Agilack/probe-net-serial/ext-display/sw-firmware/efm8bb1_defs.h

//------------------------------------------------------------------------------
// Copyright 2014 Silicon Laboratories, Inc.
// All rights reserved. This program and the accompanying materials
// are made available under the terms of the Silicon Laboratories End User
// License Agreement which accompanies this distribution, and is available at
// http://developer.silabs.com/legal/version/v11/Silicon_Labs_Software_License_Agreement.txt
// Original content and implementation provided by Silicon Laboratories.
//------------------------------------------------------------------------------
//Supported Devices:
//  EFM8BB10F2G
//  EFM8BB10F4G
//  EFM8BB10F8G
//  EFM8BB10F8G
//  EFM8BB10F8G

#ifndef SI_EFM8BB1_REGISTER_ENUMS_H
#define SI_EFM8BB1_REGISTER_ENUMS_H

//------------------------------------------------------------------------------
// ADC0AC Enums (ADC0 Accumulator Configuration @ 0xB3)
//------------------------------------------------------------------------------
#define ADC0AC_ADRPT__FMASK            0x07 ///< Repeat Count                                      
#define ADC0AC_ADRPT__SHIFT            0x00 ///< Repeat Count                                      
#define ADC0AC_ADRPT__ACC_1            0x00 ///< Perform and Accumulate 1 conversion (not used in  
                                            ///< 12-bit mode).                                     
#define ADC0AC_ADRPT__ACC_4            0x01 ///< Perform and Accumulate 4 conversions (1 conversion
                                            ///< in 12-bit mode).                                  
#define ADC0AC_ADRPT__ACC_8            0x02 ///< Perform and Accumulate 8 conversions (2           
                                            ///< conversions in 12-bit mode).                      
#define ADC0AC_ADRPT__ACC_16           0x03 ///< Perform and Accumulate 16 conversions (4          
                                            ///< conversions in 12-bit mode).                      
#define ADC0AC_ADRPT__ACC_32           0x04 ///< Perform and Accumulate 32 conversions (8          
                                            ///< conversions in 12-bit mode).                      
#define ADC0AC_ADRPT__ACC_64           0x05 ///< Perform and Accumulate 64 conversions (16         
                                            ///< conversions in 12-bit mode).                      
                                                                                                   
#define ADC0AC_ADSJST__FMASK           0x38 ///< Accumulator Shift and Justify                     
#define ADC0AC_ADSJST__SHIFT           0x03 ///< Accumulator Shift and Justify                     
#define ADC0AC_ADSJST__RIGHT_NO_SHIFT  0x00 ///< Right justified. No shifting applied.             
#define ADC0AC_ADSJST__RIGHT_SHIFT_1   0x08 ///< Right justified. Shifted right by 1 bit.          
#define ADC0AC_ADSJST__RIGHT_SHIFT_2   0x10 ///< Right justified. Shifted right by 2 bits.         
#define ADC0AC_ADSJST__RIGHT_SHIFT_3   0x18 ///< Right justified. Shifted right by 3 bits.         
#define ADC0AC_ADSJST__LEFT_NO_SHIFT   0x20 ///< Left justified. No shifting applied.              
                                                                                                   
#define ADC0AC_ADAE__BMASK             0x40 ///< Accumulate Enable                                 
#define ADC0AC_ADAE__SHIFT             0x06 ///< Accumulate Enable                                 
#define ADC0AC_ADAE__ACC_DISABLED      0x00 ///< ADC0H:ADC0L contain the result of the latest      
                                            ///< conversion when Burst Mode is disabled.           
#define ADC0AC_ADAE__ACC_ENABLED       0x40 ///< ADC0H:ADC0L contain the accumulated conversion    
                                            ///< results when Burst Mode is disabled. Firmware must
                                            ///< write 0x0000 to ADC0H:ADC0L to clear the          
                                            ///< accumulated result.                               
                                                                                                   
#define ADC0AC_AD12BE__BMASK           0x80 ///< 12-Bit Mode Enable                                
#define ADC0AC_AD12BE__SHIFT           0x07 ///< 12-Bit Mode Enable                                
#define ADC0AC_AD12BE__12_BIT_DISABLED 0x00 ///< Disable 12-bit mode.                              
#define ADC0AC_AD12BE__12_BIT_ENABLED  0x80 ///< Enable 12-bit mode.                               
                                                                                                   
//------------------------------------------------------------------------------
// ADC0CF Enums (ADC0 Configuration @ 0xBC)
//------------------------------------------------------------------------------
#define ADC0CF_ADGN__BMASK         0x01 ///< Gain Control                                      
#define ADC0CF_ADGN__SHIFT         0x00 ///< Gain Control                                      
#define ADC0CF_ADGN__GAIN_0P5      0x00 ///< The on-chip PGA gain is 0.5.                      
#define ADC0CF_ADGN__GAIN_1        0x01 ///< The on-chip PGA gain is 1.                        
                                                                                               
#define ADC0CF_ADTM__BMASK         0x02 ///< Track Mode                                        
#define ADC0CF_ADTM__SHIFT         0x01 ///< Track Mode                                        
#define ADC0CF_ADTM__TRACK_NORMAL  0x00 ///< Normal Track Mode. When ADC0 is enabled,          
                                        ///< conversion begins immediately following the start-
                                        ///< of-conversion signal.                             
#define ADC0CF_ADTM__TRACK_DELAYED 0x02 ///< Delayed Track Mode. When ADC0 is enabled,         
                                        ///< conversion begins 4 SAR clock cycles following the
                                        ///< start-of-conversion signal. The ADC is allowed to 
                                        ///< track during this time.                           
                                                                                               
#define ADC0CF_AD8BE__BMASK        0x04 ///< 8-Bit Mode Enable                                 
#define ADC0CF_AD8BE__SHIFT        0x02 ///< 8-Bit Mode Enable                                 
#define ADC0CF_AD8BE__NORMAL       0x00 ///< ADC0 operates in 10-bit or 12-bit mode (normal    
                                        ///< operation).                                       
#define ADC0CF_AD8BE__8_BIT        0x04 ///< ADC0 operates in 8-bit mode.                      
                                                                                               
#define ADC0CF_ADSC__FMASK         0xF8 ///< SAR Clock Divider                                 
#define ADC0CF_ADSC__SHIFT         0x03 ///< SAR Clock Divider                                 
                                                                                               
//------------------------------------------------------------------------------
// ADC0CN0 Enums (ADC0 Control 0 @ 0xE8)
//------------------------------------------------------------------------------
#define ADC0CN0_ADCM__FMASK            0x07 ///< Start of Conversion Mode Select                   
#define ADC0CN0_ADCM__SHIFT            0x00 ///< Start of Conversion Mode Select                   
#define ADC0CN0_ADCM__ADBUSY           0x00 ///< ADC0 conversion initiated on write of 1 to ADBUSY.
#define ADC0CN0_ADCM__TIMER0           0x01 ///< ADC0 conversion initiated on overflow of Timer 0. 
#define ADC0CN0_ADCM__TIMER2           0x02 ///< ADC0 conversion initiated on overflow of Timer 2. 
#define ADC0CN0_ADCM__TIMER3           0x03 ///< ADC0 conversion initiated on overflow of Timer 3. 
#define ADC0CN0_ADCM__CNVSTR           0x04 ///< ADC0 conversion initiated on rising edge of       
                                            ///< CNVSTR.                                           
                                                                                                   
#define ADC0CN0_ADWINT__BMASK          0x08 ///< Window Compare Interrupt Flag                     
#define ADC0CN0_ADWINT__SHIFT          0x03 ///< Window Compare Interrupt Flag                     
#define ADC0CN0_ADWINT__NOT_SET        0x00 ///< An ADC window compare event did not occur.        
#define ADC0CN0_ADWINT__SET            0x08 ///< An ADC window compare event occurred.             
                                                                                                   
#define ADC0CN0_ADBUSY__BMASK          0x10 ///< ADC Busy                                          
#define ADC0CN0_ADBUSY__SHIFT          0x04 ///< ADC Busy                                          
#define ADC0CN0_ADBUSY__NOT_SET        0x00 ///< An ADC0 conversion is not currently in progress.  
#define ADC0CN0_ADBUSY__SET            0x10 ///< ADC0 conversion is in progress or start an ADC0   
                                            ///< conversion.                                       
                                                                                                   
#define ADC0CN0_ADINT__BMASK           0x20 ///< Conversion Complete Interrupt Flag                
#define ADC0CN0_ADINT__SHIFT           0x05 ///< Conversion Complete Interrupt Flag                
#define ADC0CN0_ADINT__NOT_SET         0x00 ///< ADC0 has not completed a conversion since the last
                                            ///< time ADINT was cleared.                           
#define ADC0CN0_ADINT__SET             0x20 ///< ADC0 completed a data conversion.                 
                                                                                                   
#define ADC0CN0_ADBMEN__BMASK          0x40 ///< Burst Mode Enable                                 
#define ADC0CN0_ADBMEN__SHIFT          0x06 ///< Burst Mode Enable                                 
#define ADC0CN0_ADBMEN__BURST_DISABLED 0x00 ///< Disable ADC0 burst mode.                          
#define ADC0CN0_ADBMEN__BURST_ENABLED  0x40 ///< Enable ADC0 burst mode.                           
                                                                                                   
#define ADC0CN0_ADEN__BMASK            0x80 ///< ADC Enable                                        
#define ADC0CN0_ADEN__SHIFT            0x07 ///< ADC Enable                                        
#define ADC0CN0_ADEN__DISABLED         0x00 ///< Disable ADC0 (low-power shutdown).                
#define ADC0CN0_ADEN__ENABLED          0x80 ///< Enable ADC0 (active and ready for data            
                                            ///< conversions).                                     
                                                                                                   
//------------------------------------------------------------------------------
// ADC0CN1 Enums (ADC0 Control 1 @ 0xB2)
//------------------------------------------------------------------------------
#define ADC0CN1_ADCMBE__BMASK              0x01 ///< Common Mode Buffer Enable                         
#define ADC0CN1_ADCMBE__SHIFT              0x00 ///< Common Mode Buffer Enable                         
#define ADC0CN1_ADCMBE__CM_BUFFER_DISABLED 0x00 ///< Disable the common mode buffer. This setting      
                                                ///< should be used only if the tracking time of the   
                                                ///< signal is greater than 1.5 us.                    
#define ADC0CN1_ADCMBE__CM_BUFFER_ENABLED  0x01 ///< Enable the common mode buffer. This setting should
                                                ///< be used in most cases, and will give the best     
                                                ///< dynamic ADC performance. The common mode buffer   
                                                ///< must be enabled if signal tracking time is less   
                                                ///< than or equal to 1.5 us.                          
                                                                                                       
//------------------------------------------------------------------------------
// ADC0GTH Enums (ADC0 Greater-Than High Byte @ 0xC4)
//------------------------------------------------------------------------------
#define ADC0GTH_ADC0GTH__FMASK 0xFF ///< Greater-Than High Byte
#define ADC0GTH_ADC0GTH__SHIFT 0x00 ///< Greater-Than High Byte
                                                               
//------------------------------------------------------------------------------
// ADC0GTL Enums (ADC0 Greater-Than Low Byte @ 0xC3)
//------------------------------------------------------------------------------
#define ADC0GTL_ADC0GTL__FMASK 0xFF ///< Greater-Than Low Byte
#define ADC0GTL_ADC0GTL__SHIFT 0x00 ///< Greater-Than Low Byte
                                                              
//------------------------------------------------------------------------------
// ADC0H Enums (ADC0 Data Word High Byte @ 0xBE)
//------------------------------------------------------------------------------
#define ADC0H_ADC0H__FMASK 0xFF ///< Data Word High Byte
#define ADC0H_ADC0H__SHIFT 0x00 ///< Data Word High Byte
                                                        
//------------------------------------------------------------------------------
// ADC0L Enums (ADC0 Data Word Low Byte @ 0xBD)
//------------------------------------------------------------------------------
#define ADC0L_ADC0L__FMASK 0xFF ///< Data Word Low Byte
#define ADC0L_ADC0L__SHIFT 0x00 ///< Data Word Low Byte
                                                       
//------------------------------------------------------------------------------
// ADC0LTH Enums (ADC0 Less-Than High Byte @ 0xC6)
//------------------------------------------------------------------------------
#define ADC0LTH_ADC0LTH__FMASK 0xFF ///< Less-Than High Byte
#define ADC0LTH_ADC0LTH__SHIFT 0x00 ///< Less-Than High Byte
                                                            
//------------------------------------------------------------------------------
// ADC0LTL Enums (ADC0 Less-Than Low Byte @ 0xC5)
//------------------------------------------------------------------------------
#define ADC0LTL_ADC0LTL__FMASK 0xFF ///< Less-Than Low Byte
#define ADC0LTL_ADC0LTL__SHIFT 0x00 ///< Less-Than Low Byte
                                                           
//------------------------------------------------------------------------------
// ADC0MX Enums (ADC0 Multiplexer Selection @ 0xBB)
//------------------------------------------------------------------------------
#define ADC0MX_ADC0MX__FMASK   0x1F ///< AMUX0 Positive Input Selection
#define ADC0MX_ADC0MX__SHIFT   0x00 ///< AMUX0 Positive Input Selection
#define ADC0MX_ADC0MX__ADC0P0  0x00 ///< Select ADC0.0.                
#define ADC0MX_ADC0MX__ADC0P1  0x01 ///< Select ADC0.1.                
#define ADC0MX_ADC0MX__ADC0P2  0x02 ///< Select ADC0.2.                
#define ADC0MX_ADC0MX__ADC0P3  0x03 ///< Select ADC0.3.                
#define ADC0MX_ADC0MX__ADC0P4  0x04 ///< Select ADC0.4.                
#define ADC0MX_ADC0MX__ADC0P5  0x05 ///< Select ADC0.5.                
#define ADC0MX_ADC0MX__ADC0P6  0x06 ///< Select ADC0.6.                
#define ADC0MX_ADC0MX__ADC0P7  0x07 ///< Select ADC0.7.                
#define ADC0MX_ADC0MX__ADC0P8  0x08 ///< Select ADC0.8.                
#define ADC0MX_ADC0MX__ADC0P9  0x09 ///< Select ADC0.9.                
#define ADC0MX_ADC0MX__ADC0P10 0x0A ///< Select ADC0.10.               
#define ADC0MX_ADC0MX__ADC0P11 0x0B ///< Select ADC0.11.               
#define ADC0MX_ADC0MX__ADC0P12 0x0C ///< Select ADC0.12.               
#define ADC0MX_ADC0MX__ADC0P13 0x0D ///< Select ADC0.13.               
#define ADC0MX_ADC0MX__ADC0P14 0x0E ///< Select ADC0.14.               
#define ADC0MX_ADC0MX__ADC0P15 0x0F ///< Select ADC0.15.               
#define ADC0MX_ADC0MX__TEMP    0x10 ///< Select ADC0.16.               
#define ADC0MX_ADC0MX__LDO_OUT 0x11 ///< Select ADC0.17.               
#define ADC0MX_ADC0MX__VDD     0x12 ///< Select ADC0.18.               
#define ADC0MX_ADC0MX__GND     0x13 ///< Select ADC0.19.               
#define ADC0MX_ADC0MX__NONE    0x1F ///< No input selected.            
                                                                       
//------------------------------------------------------------------------------
// ADC0PWR Enums (ADC0 Power Control @ 0xDF)
//------------------------------------------------------------------------------
#define ADC0PWR_ADPWR__FMASK                 0x0F ///< Burst Mode Power Up Time                         
#define ADC0PWR_ADPWR__SHIFT                 0x00 ///< Burst Mode Power Up Time                         
                                                                                                        
#define ADC0PWR_ADLPM__BMASK                 0x10 ///< Low Power Mode Enable                            
#define ADC0PWR_ADLPM__SHIFT                 0x04 ///< Low Power Mode Enable                            
#define ADC0PWR_ADLPM__LP_BUFFER_DISABLED    0x00 ///< Disable low power mode.                          
#define ADC0PWR_ADLPM__LP_BUFFER_ENABLED     0x10 ///< Enable low power mode (requires extended tracking
                                                  ///< time).                                           
                                                                                                        
#define ADC0PWR_ADMXLP__BMASK                0x20 ///< Mux and Reference Low Power Mode Enable          
#define ADC0PWR_ADMXLP__SHIFT                0x05 ///< Mux and Reference Low Power Mode Enable          
#define ADC0PWR_ADMXLP__LP_MUX_VREF_DISABLED 0x00 ///< Low power mode disabled.                         
#define ADC0PWR_ADMXLP__LP_MUX_VREF_ENABLED  0x20 ///< Low power mode enabled (SAR clock < 4 MHz).      
                                                                                                        
#define ADC0PWR_ADBIAS__FMASK                0xC0 ///< Bias Power Select                                
#define ADC0PWR_ADBIAS__SHIFT                0x06 ///< Bias Power Select                                
#define ADC0PWR_ADBIAS__MODE0                0x00 ///< Select bias current mode 0. Recommended to use   
                                                  ///< modes 1, 2, or 3.                                
#define ADC0PWR_ADBIAS__MODE1                0x40 ///< Select bias current mode 1 (SARCLK <= 16 MHz).   
#define ADC0PWR_ADBIAS__MODE2                0x80 ///< Select bias current mode 2.                      
#define ADC0PWR_ADBIAS__MODE3                0xC0 ///< Select bias current mode 3 (SARCLK <= 4 MHz).    
                                                                                                        
//------------------------------------------------------------------------------
// ADC0TK Enums (ADC0 Burst Mode Track Time @ 0xB9)
//------------------------------------------------------------------------------
#define ADC0TK_ADTK__FMASK         0x3F ///< Burst Mode Tracking Time                       
#define ADC0TK_ADTK__SHIFT         0x00 ///< Burst Mode Tracking Time                       
                                                                                            
#define ADC0TK_AD12SM__BMASK       0x80 ///< 12-Bit Sampling Mode                           
#define ADC0TK_AD12SM__SHIFT       0x07 ///< 12-Bit Sampling Mode                           
#define ADC0TK_AD12SM__SAMPLE_FOUR 0x00 ///< The ADC will re-track and sample the input four
                                        ///< times during a 12-bit conversion.              
#define ADC0TK_AD12SM__SAMPLE_ONCE 0x80 ///< The ADC will sample the input once at the      
                                        ///< beginning of each 12-bit conversion. The ADTK  
                                        ///< field can be set to 63 to maximize throughput. 
                                                                                            
//------------------------------------------------------------------------------
// ACC Enums (Accumulator @ 0xE0)
//------------------------------------------------------------------------------
#define ACC_ACC__FMASK 0xFF ///< Accumulator
#define ACC_ACC__SHIFT 0x00 ///< Accumulator
                                            
//------------------------------------------------------------------------------
// B Enums (B Register @ 0xF0)
//------------------------------------------------------------------------------
#define B_B__FMASK 0xFF ///< B Register
#define B_B__SHIFT 0x00 ///< B Register
                                       
//------------------------------------------------------------------------------
// DPH Enums (Data Pointer High @ 0x83)
//------------------------------------------------------------------------------
#define DPH_DPH__FMASK 0xFF ///< Data Pointer High
#define DPH_DPH__SHIFT 0x00 ///< Data Pointer High
                                                  
//------------------------------------------------------------------------------
// DPL Enums (Data Pointer Low @ 0x82)
//------------------------------------------------------------------------------
#define DPL_DPL__FMASK 0xFF ///< Data Pointer Low
#define DPL_DPL__SHIFT 0x00 ///< Data Pointer Low
                                                 
//------------------------------------------------------------------------------
// PSW Enums (Program Status Word @ 0xD0)
//------------------------------------------------------------------------------
#define PSW_PARITY__BMASK   0x01 ///< Parity Flag                                       
#define PSW_PARITY__SHIFT   0x00 ///< Parity Flag                                       
#define PSW_PARITY__NOT_SET 0x00 ///< The sum of the 8 bits in the accumulator is even. 
#define PSW_PARITY__SET     0x01 ///< The sum of the 8 bits in the accumulator is odd.  
                                                                                        
#define PSW_F1__BMASK       0x02 ///< User Flag 1                                       
#define PSW_F1__SHIFT       0x01 ///< User Flag 1                                       
#define PSW_F1__NOT_SET     0x00 ///< Flag is not set.                                  
#define PSW_F1__SET         0x02 ///< Flag is set.                                      
                                                                                        
#define PSW_OV__BMASK       0x04 ///< Overflow Flag                                     
#define PSW_OV__SHIFT       0x02 ///< Overflow Flag                                     
#define PSW_OV__NOT_SET     0x00 ///< An overflow did not occur.                        
#define PSW_OV__SET         0x04 ///< An overflow occurred.                             
                                                                                        
#define PSW_RS__FMASK       0x18 ///< Register Bank Select                              
#define PSW_RS__SHIFT       0x03 ///< Register Bank Select                              
#define PSW_RS__BANK0       0x00 ///< Bank 0, Addresses 0x00-0x07                       
#define PSW_RS__BANK1       0x08 ///< Bank 1, Addresses 0x08-0x0F                       
#define PSW_RS__BANK2       0x10 ///< Bank 2, Addresses 0x10-0x17                       
#define PSW_RS__BANK3       0x18 ///< Bank 3, Addresses 0x18-0x1F                       
                                                                                        
#define PSW_F0__BMASK       0x20 ///< User Flag 0                                       
#define PSW_F0__SHIFT       0x05 ///< User Flag 0                                       
#define PSW_F0__NOT_SET     0x00 ///< Flag is not set.                                  
#define PSW_F0__SET         0x20 ///< Flag is set.                                      
                                                                                        
#define PSW_AC__BMASK       0x40 ///< Auxiliary Carry Flag                              
#define PSW_AC__SHIFT       0x06 ///< Auxiliary Carry Flag                              
#define PSW_AC__NOT_SET     0x00 ///< A carry into (addition) or borrow from            
                                 ///< (subtraction) the high order nibble did not occur.
#define PSW_AC__SET         0x40 ///< A carry into (addition) or borrow from            
                                 ///< (subtraction) the high order nibble occurred.     
                                                                                        
#define PSW_CY__BMASK       0x80 ///< Carry Flag                                        
#define PSW_CY__SHIFT       0x07 ///< Carry Flag                                        
#define PSW_CY__NOT_SET     0x00 ///< A carry (addition) or borrow (subtraction) did not
                                 ///< occur.                                            
#define PSW_CY__SET         0x80 ///< A carry (addition) or borrow (subtraction)        
                                 ///< occurred.                                         
                                                                                        
//------------------------------------------------------------------------------
// SP Enums (Stack Pointer @ 0x81)
//------------------------------------------------------------------------------
#define SP_SP__FMASK 0xFF ///< Stack Pointer
#define SP_SP__SHIFT 0x00 ///< Stack Pointer
                                            
//------------------------------------------------------------------------------
// CLKSEL Enums (Clock Select @ 0xA9)
//------------------------------------------------------------------------------
#define CLKSEL_CLKSL__FMASK           0x03 ///< Clock Source Select                             
#define CLKSEL_CLKSL__SHIFT           0x00 ///< Clock Source Select                             
#define CLKSEL_CLKSL__HFOSC           0x00 ///< Clock derived from the Internal High-Frequency  
                                           ///< Oscillator.                                     
#define CLKSEL_CLKSL__EXTOSC          0x01 ///< Clock derived from the External CMOS clock      
                                           ///< circuit.                                        
#define CLKSEL_CLKSL__LFOSC           0x02 ///< Clock derived from the Internal Low-Frequency   
                                           ///< Oscillator.                                     
                                                                                                
#define CLKSEL_CLKDIV__FMASK          0x70 ///< Clock Source Divider                            
#define CLKSEL_CLKDIV__SHIFT          0x04 ///< Clock Source Divider                            
#define CLKSEL_CLKDIV__SYSCLK_DIV_1   0x00 ///< SYSCLK is equal to selected clock source divided
                                           ///< by 1.                                           
#define CLKSEL_CLKDIV__SYSCLK_DIV_2   0x10 ///< SYSCLK is equal to selected clock source divided
                                           ///< by 2.                                           
#define CLKSEL_CLKDIV__SYSCLK_DIV_4   0x20 ///< SYSCLK is equal to selected clock source divided
                                           ///< by 4.                                           
#define CLKSEL_CLKDIV__SYSCLK_DIV_8   0x30 ///< SYSCLK is equal to selected clock source divided
                                           ///< by 8.                                           
#define CLKSEL_CLKDIV__SYSCLK_DIV_16  0x40 ///< SYSCLK is equal to selected clock source divided
                                           ///< by 16.                                          
#define CLKSEL_CLKDIV__SYSCLK_DIV_32  0x50 ///< SYSCLK is equal to selected clock source divided
                                           ///< by 32.                                          
#define CLKSEL_CLKDIV__SYSCLK_DIV_64  0x60 ///< SYSCLK is equal to selected clock source divided
                                           ///< by 64.                                          
#define CLKSEL_CLKDIV__SYSCLK_DIV_128 0x70 ///< SYSCLK is equal to selected clock source divided
                                           ///< by 128.                                         
                                                                                                
//------------------------------------------------------------------------------
// CMP0CN0 Enums (Comparator 0 Control 0 @ 0x9B)
//------------------------------------------------------------------------------
#define CMP0CN0_CPHYN__FMASK                0x03 ///< Comparator Negative Hysteresis Control            
#define CMP0CN0_CPHYN__SHIFT                0x00 ///< Comparator Negative Hysteresis Control            
#define CMP0CN0_CPHYN__DISABLED             0x00 ///< Negative Hysteresis disabled.                     
#define CMP0CN0_CPHYN__ENABLED_MODE1        0x01 ///< Negative Hysteresis = Hysteresis 1.               
#define CMP0CN0_CPHYN__ENABLED_MODE2        0x02 ///< Negative Hysteresis = Hysteresis 2.               
#define CMP0CN0_CPHYN__ENABLED_MODE3        0x03 ///< Negative Hysteresis = Hysteresis 3 (Maximum).     
                                                                                                        
#define CMP0CN0_CPHYP__FMASK                0x0C ///< Comparator Positive Hysteresis Control            
#define CMP0CN0_CPHYP__SHIFT                0x02 ///< Comparator Positive Hysteresis Control            
#define CMP0CN0_CPHYP__DISABLED             0x00 ///< Positive Hysteresis disabled.                     
#define CMP0CN0_CPHYP__ENABLED_MODE1        0x04 ///< Positive Hysteresis = Hysteresis 1.               
#define CMP0CN0_CPHYP__ENABLED_MODE2        0x08 ///< Positive Hysteresis = Hysteresis 2.               
#define CMP0CN0_CPHYP__ENABLED_MODE3        0x0C ///< Positive Hysteresis = Hysteresis 3 (Maximum).     
                                                                                                        
#define CMP0CN0_CPFIF__BMASK                0x10 ///< Comparator Falling-Edge Flag                      
#define CMP0CN0_CPFIF__SHIFT                0x04 ///< Comparator Falling-Edge Flag                      
#define CMP0CN0_CPFIF__NOT_SET              0x00 ///< No comparator falling edge has occurred since this
                                                 ///< flag was last cleared.                            
#define CMP0CN0_CPFIF__FALLING_EDGE         0x10 ///< Comparator falling edge has occurred.             
                                                                                                        
#define CMP0CN0_CPRIF__BMASK                0x20 ///< Comparator Rising-Edge Flag                       
#define CMP0CN0_CPRIF__SHIFT                0x05 ///< Comparator Rising-Edge Flag                       
#define CMP0CN0_CPRIF__NOT_SET              0x00 ///< No comparator rising edge has occurred since this 
                                                 ///< flag was last cleared.                            
#define CMP0CN0_CPRIF__RISING_EDGE          0x20 ///< Comparator rising edge has occurred.              
                                                                                                        
#define CMP0CN0_CPOUT__BMASK                0x40 ///< Comparator Output State Flag                      
#define CMP0CN0_CPOUT__SHIFT                0x06 ///< Comparator Output State Flag                      
#define CMP0CN0_CPOUT__POS_LESS_THAN_NEG    0x00 ///< Voltage on CP0P < CP0N.                           
#define CMP0CN0_CPOUT__POS_GREATER_THAN_NEG 0x40 ///< Voltage on CP0P > CP0N.                           
                                                                                                        
#define CMP0CN0_CPEN__BMASK                 0x80 ///< Comparator Enable                                 
#define CMP0CN0_CPEN__SHIFT                 0x07 ///< Comparator Enable                                 
#define CMP0CN0_CPEN__DISABLED              0x00 ///< Comparator disabled.                              
#define CMP0CN0_CPEN__ENABLED               0x80 ///< Comparator enabled.                               
                                                                                                        
//------------------------------------------------------------------------------
// CMP0MD Enums (Comparator 0 Mode @ 0x9D)
//------------------------------------------------------------------------------
#define CMP0MD_CPMD__FMASK              0x03 ///< Comparator Mode Select                      
#define CMP0MD_CPMD__SHIFT              0x00 ///< Comparator Mode Select                      
#define CMP0MD_CPMD__MODE0              0x00 ///< Mode 0 (Fastest Response Time, Highest Power
                                             ///< Consumption)                                
#define CMP0MD_CPMD__MODE1              0x01 ///< Mode 1                                      
#define CMP0MD_CPMD__MODE2              0x02 ///< Mode 2                                      
#define CMP0MD_CPMD__MODE3              0x03 ///< Mode 3 (Slowest Response Time, Lowest Power 
                                             ///< Consumption)                                
                                                                                              
#define CMP0MD_CPFIE__BMASK             0x10 ///< Comparator Falling-Edge Interrupt Enable    
#define CMP0MD_CPFIE__SHIFT             0x04 ///< Comparator Falling-Edge Interrupt Enable    
#define CMP0MD_CPFIE__FALL_INT_DISABLED 0x00 ///< Comparator falling-edge interrupt disabled. 
#define CMP0MD_CPFIE__FALL_INT_ENABLED  0x10 ///< Comparator falling-edge interrupt enabled.  
                                                                                              
#define CMP0MD_CPRIE__BMASK             0x20 ///< Comparator Rising-Edge Interrupt Enable     
#define CMP0MD_CPRIE__SHIFT             0x05 ///< Comparator Rising-Edge Interrupt Enable     
#define CMP0MD_CPRIE__RISE_INT_DISABLED 0x00 ///< Comparator rising-edge interrupt disabled.  
#define CMP0MD_CPRIE__RISE_INT_ENABLED  0x20 ///< Comparator rising-edge interrupt enabled.   
                                                                                              
#define CMP0MD_CPLOUT__BMASK            0x80 ///< Comparator Latched Output Flag              
#define CMP0MD_CPLOUT__SHIFT            0x07 ///< Comparator Latched Output Flag              
#define CMP0MD_CPLOUT__LOW              0x00 ///< Comparator output was logic low at last PCA 
                                             ///< overflow.                                   
#define CMP0MD_CPLOUT__HIGH             0x80 ///< Comparator output was logic high at last PCA
                                             ///< overflow.                                   
                                                                                              
//------------------------------------------------------------------------------
// CMP0MX Enums (Comparator 0 Multiplexer Selection @ 0x9F)
//------------------------------------------------------------------------------
#define CMP0MX_CMXP__FMASK   0x0F ///< Comparator Positive Input MUX Selection
#define CMP0MX_CMXP__SHIFT   0x00 ///< Comparator Positive Input MUX Selection
#define CMP0MX_CMXP__CMP0P0  0x00 ///< External pin CMP0P.0.                  
#define CMP0MX_CMXP__CMP0P1  0x01 ///< External pin CMP0P.1.                  
#define CMP0MX_CMXP__CMP0P2  0x02 ///< External pin CMP0P.2.                  
#define CMP0MX_CMXP__CMP0P3  0x03 ///< External pin CMP0P.3.                  
#define CMP0MX_CMXP__CMP0P4  0x04 ///< External pin CMP0P.4.                  
#define CMP0MX_CMXP__CMP0P5  0x05 ///< External pin CMP0P.5.                  
#define CMP0MX_CMXP__CMP0P6  0x06 ///< External pin CMP0P.6.                  
#define CMP0MX_CMXP__CMP0P7  0x07 ///< External pin CMP0P.7.                  
#define CMP0MX_CMXP__LDO_OUT 0x08 ///< External pin CMP0P.8.                  
#define CMP0MX_CMXP__NONE    0x0F ///< No input selected.                     
                                                                              
#define CMP0MX_CMXN__FMASK   0xF0 ///< Comparator Negative Input MUX Selection
#define CMP0MX_CMXN__SHIFT   0x04 ///< Comparator Negative Input MUX Selection
#define CMP0MX_CMXN__CMP0N0  0x00 ///< External pin CMP0N.0.                  
#define CMP0MX_CMXN__CMP0N1  0x10 ///< External pin CMP0N.1.                  
#define CMP0MX_CMXN__CMP0N2  0x20 ///< External pin CMP0N.2.                  
#define CMP0MX_CMXN__CMP0N3  0x30 ///< External pin CMP0N.3.                  
#define CMP0MX_CMXN__CMP0N4  0x40 ///< External pin CMP0N.4.                  
#define CMP0MX_CMXN__CMP0N5  0x50 ///< External pin CMP0N.5.                  
#define CMP0MX_CMXN__CMP0N6  0x60 ///< External pin CMP0N.6.                  
#define CMP0MX_CMXN__CMP0N7  0x70 ///< External pin CMP0N.7.                  
#define CMP0MX_CMXN__GND     0x80 ///< External pin CMP0N.8.                  
#define CMP0MX_CMXN__NONE    0xF0 ///< No input selected.                     
                                                                              
//------------------------------------------------------------------------------
// CMP1CN0 Enums (Comparator 1 Control 0 @ 0xBF)
//------------------------------------------------------------------------------
#define CMP1CN0_CPHYN__FMASK                0x03 ///< Comparator Negative Hysteresis Control            
#define CMP1CN0_CPHYN__SHIFT                0x00 ///< Comparator Negative Hysteresis Control            
#define CMP1CN0_CPHYN__DISABLED             0x00 ///< Negative Hysteresis disabled.                     
#define CMP1CN0_CPHYN__ENABLED_MODE1        0x01 ///< Negative Hysteresis = Hysteresis 1.               
#define CMP1CN0_CPHYN__ENABLED_MODE2        0x02 ///< Negative Hysteresis = Hysteresis 2.               
#define CMP1CN0_CPHYN__ENABLED_MODE3        0x03 ///< Negative Hysteresis = Hysteresis 3 (Maximum).     
                                                                                                        
#define CMP1CN0_CPHYP__FMASK                0x0C ///< Comparator Positive Hysteresis Control            
#define CMP1CN0_CPHYP__SHIFT                0x02 ///< Comparator Positive Hysteresis Control            
#define CMP1CN0_CPHYP__DISABLED             0x00 ///< Positive Hysteresis disabled.                     
#define CMP1CN0_CPHYP__ENABLED_MODE1        0x04 ///< Positive Hysteresis = Hysteresis 1.               
#define CMP1CN0_CPHYP__ENABLED_MODE2        0x08 ///< Positive Hysteresis = Hysteresis 2.               
#define CMP1CN0_CPHYP__ENABLED_MODE3        0x0C ///< Positive Hysteresis = Hysteresis 3 (Maximum).     
                                                                                                        
#define CMP1CN0_CPFIF__BMASK                0x10 ///< Comparator Falling-Edge Flag                      
#define CMP1CN0_CPFIF__SHIFT                0x04 ///< Comparator Falling-Edge Flag                      
#define CMP1CN0_CPFIF__NOT_SET              0x00 ///< No comparator falling edge has occurred since this
                                                 ///< flag was last cleared.                            
#define CMP1CN0_CPFIF__FALLING_EDGE         0x10 ///< Comparator falling edge has occurred.             
                                                                                                        
#define CMP1CN0_CPRIF__BMASK                0x20 ///< Comparator Rising-Edge Flag                       
#define CMP1CN0_CPRIF__SHIFT                0x05 ///< Comparator Rising-Edge Flag                       
#define CMP1CN0_CPRIF__NOT_SET              0x00 ///< No comparator rising edge has occurred since this 
                                                 ///< flag was last cleared.                            
#define CMP1CN0_CPRIF__RISING_EDGE          0x20 ///< Comparator rising edge has occurred.              
                                                                                                        
#define CMP1CN0_CPOUT__BMASK                0x40 ///< Comparator Output State Flag                      
#define CMP1CN0_CPOUT__SHIFT                0x06 ///< Comparator Output State Flag                      
#define CMP1CN0_CPOUT__POS_LESS_THAN_NEG    0x00 ///< Voltage on CP1P < CP1N.                           
#define CMP1CN0_CPOUT__POS_GREATER_THAN_NEG 0x40 ///< Voltage on CP1P > CP1N.                           
                                                                                                        
#define CMP1CN0_CPEN__BMASK                 0x80 ///< Comparator Enable                                 
#define CMP1CN0_CPEN__SHIFT                 0x07 ///< Comparator Enable                                 
#define CMP1CN0_CPEN__DISABLED              0x00 ///< Comparator disabled.                              
#define CMP1CN0_CPEN__ENABLED               0x80 ///< Comparator enabled.                               
                                                                                                        
//------------------------------------------------------------------------------
// CMP1MD Enums (Comparator 1 Mode @ 0xAB)
//------------------------------------------------------------------------------
#define CMP1MD_CPMD__FMASK              0x03 ///< Comparator Mode Select                      
#define CMP1MD_CPMD__SHIFT              0x00 ///< Comparator Mode Select                      
#define CMP1MD_CPMD__MODE0              0x00 ///< Mode 0 (Fastest Response Time, Highest Power
                                             ///< Consumption)                                
#define CMP1MD_CPMD__MODE1              0x01 ///< Mode 1                                      
#define CMP1MD_CPMD__MODE2              0x02 ///< Mode 2                                      
#define CMP1MD_CPMD__MODE3              0x03 ///< Mode 3 (Slowest Response Time, Lowest Power 
                                             ///< Consumption)                                
                                                                                              
#define CMP1MD_CPFIE__BMASK             0x10 ///< Comparator Falling-Edge Interrupt Enable    
#define CMP1MD_CPFIE__SHIFT             0x04 ///< Comparator Falling-Edge Interrupt Enable    
#define CMP1MD_CPFIE__FALL_INT_DISABLED 0x00 ///< Comparator falling-edge interrupt disabled. 
#define CMP1MD_CPFIE__FALL_INT_ENABLED  0x10 ///< Comparator falling-edge interrupt enabled.  
                                                                                              
#define CMP1MD_CPRIE__BMASK             0x20 ///< Comparator Rising-Edge Interrupt Enable     
#define CMP1MD_CPRIE__SHIFT             0x05 ///< Comparator Rising-Edge Interrupt Enable     
#define CMP1MD_CPRIE__RISE_INT_DISABLED 0x00 ///< Comparator rising-edge interrupt disabled.  
#define CMP1MD_CPRIE__RISE_INT_ENABLED  0x20 ///< Comparator rising-edge interrupt enabled.   
                                                                                              
#define CMP1MD_CPLOUT__BMASK            0x80 ///< Comparator Latched Output Flag              
#define CMP1MD_CPLOUT__SHIFT            0x07 ///< Comparator Latched Output Flag              
#define CMP1MD_CPLOUT__LOW              0x00 ///< Comparator output was logic low at last PCA 
                                             ///< overflow.                                   
#define CMP1MD_CPLOUT__HIGH             0x80 ///< Comparator output was logic high at last PCA
                                             ///< overflow.                                   
                                                                                              
//------------------------------------------------------------------------------
// CMP1MX Enums (Comparator 1 Multiplexer Selection @ 0xAA)
//------------------------------------------------------------------------------
#define CMP1MX_CMXP__FMASK   0x0F ///< Comparator Positive Input MUX Selection
#define CMP1MX_CMXP__SHIFT   0x00 ///< Comparator Positive Input MUX Selection
#define CMP1MX_CMXP__CMP1P0  0x00 ///< External pin CMP1P.0.                  
#define CMP1MX_CMXP__CMP1P1  0x01 ///< External pin CMP1P.1.                  
#define CMP1MX_CMXP__CMP1P2  0x02 ///< External pin CMP1P.2.                  
#define CMP1MX_CMXP__CMP1P3  0x03 ///< External pin CMP1P.3.                  
#define CMP1MX_CMXP__CMP1P4  0x04 ///< External pin CMP1P.4.                  
#define CMP1MX_CMXP__CMP1P5  0x05 ///< External pin CMP1P.5.                  
#define CMP1MX_CMXP__CMP1P6  0x06 ///< External pin CMP1P.6.                  
#define CMP1MX_CMXP__CMP1P7  0x07 ///< External pin CMP1P.7.                  
#define CMP1MX_CMXP__LDO_OUT 0x08 ///< External pin CMP1P.8.                  
#define CMP1MX_CMXP__NONE    0x0F ///< No input selected.                     
                                                                              
#define CMP1MX_CMXN__FMASK   0xF0 ///< Comparator Negative Input MUX Selection
#define CMP1MX_CMXN__SHIFT   0x04 ///< Comparator Negative Input MUX Selection
#define CMP1MX_CMXN__CMP1N0  0x00 ///< External pin CMP1N.0.                  
#define CMP1MX_CMXN__CMP1N1  0x10 ///< External pin CMP1N.1.                  
#define CMP1MX_CMXN__CMP1N2  0x20 ///< External pin CMP1N.2.                  
#define CMP1MX_CMXN__CMP1N3  0x30 ///< External pin CMP1N.3.                  
#define CMP1MX_CMXN__CMP1N4  0x40 ///< External pin CMP1N.4.                  
#define CMP1MX_CMXN__CMP1N5  0x50 ///< External pin CMP1N.5.                  
#define CMP1MX_CMXN__CMP1N6  0x60 ///< External pin CMP1N.6.                  
#define CMP1MX_CMXN__CMP1N7  0x70 ///< External pin CMP1N.7.                  
#define CMP1MX_CMXN__GND     0x80 ///< External pin CMP1N.8.                  
#define CMP1MX_CMXN__NONE    0xF0 ///< No input selected.                     
                                                                              
//------------------------------------------------------------------------------
// CRC0AUTO Enums (CRC0 Automatic Control @ 0xD2)
//------------------------------------------------------------------------------
#define CRC0AUTO_CRCST__FMASK     0x3F ///< Automatic CRC Calculation Starting Block  
#define CRC0AUTO_CRCST__SHIFT     0x00 ///< Automatic CRC Calculation Starting Block  
                                                                                      
#define CRC0AUTO_AUTOEN__BMASK    0x80 ///< Automatic CRC Calculation Enable          
#define CRC0AUTO_AUTOEN__SHIFT    0x07 ///< Automatic CRC Calculation Enable          
#define CRC0AUTO_AUTOEN__DISABLED 0x00 ///< Disable automatic CRC operations on flash.
#define CRC0AUTO_AUTOEN__ENABLED  0x80 ///< Enable automatic CRC operations on flash. 
                                                                                      
//------------------------------------------------------------------------------
// CRC0CN0 Enums (CRC0 Control 0 @ 0xCE)
//------------------------------------------------------------------------------
#define CRC0CN0_CRCPNT__BMASK        0x01 ///< CRC Result Pointer                               
#define CRC0CN0_CRCPNT__SHIFT        0x00 ///< CRC Result Pointer                               
#define CRC0CN0_CRCPNT__ACCESS_LOWER 0x00 ///< CRC0DAT accesses bits 7-0 of the 16-bit CRC      
                                          ///< result.                                          
#define CRC0CN0_CRCPNT__ACCESS_UPPER 0x01 ///< CRC0DAT accesses bits 15-8 of the 16-bit CRC     
                                          ///< result.                                          
                                                                                                
#define CRC0CN0_CRCVAL__BMASK        0x04 ///< CRC Initialization Value                         
#define CRC0CN0_CRCVAL__SHIFT        0x02 ///< CRC Initialization Value                         
#define CRC0CN0_CRCVAL__SET_ZEROES   0x00 ///< CRC result is set to 0x0000 on write of 1 to     
                                          ///< CRCINIT.                                         
#define CRC0CN0_CRCVAL__SET_ONES     0x04 ///< CRC result is set to 0xFFFF on write of 1 to     
                                          ///< CRCINIT.                                         
                                                                                                
#define CRC0CN0_CRCINIT__BMASK       0x08 ///< CRC Initialization Enable                        
#define CRC0CN0_CRCINIT__SHIFT       0x03 ///< CRC Initialization Enable                        
#define CRC0CN0_CRCINIT__DO_NOT_INIT 0x00 ///< Do not initialize the CRC result.                
#define CRC0CN0_CRCINIT__INIT        0x08 ///< Initialize the CRC result to ones or zeroes vased
                                          ///< on the value of CRCVAL.                          
                                                                                                
//------------------------------------------------------------------------------
// CRC0CNT Enums (CRC0 Automatic Flash Sector Count @ 0xD3)
//------------------------------------------------------------------------------
#define CRC0CNT_CRCCNT__FMASK  0x1F ///< Automatic CRC Calculation Block Count
#define CRC0CNT_CRCCNT__SHIFT  0x00 ///< Automatic CRC Calculation Block Count
                                                                              
#define CRC0CNT_CRCDN__BMASK   0x80 ///< Automatic CRC Calculation Complete   
#define CRC0CNT_CRCDN__SHIFT   0x07 ///< Automatic CRC Calculation Complete   
#define CRC0CNT_CRCDN__NOT_SET 0x00 ///< A CRC calculation is in progress.    
#define CRC0CNT_CRCDN__SET     0x80 ///< A CRC calculation is not in progress.
                                                                              
//------------------------------------------------------------------------------
// CRC0DAT Enums (CRC0 Data Output @ 0xDE)
//------------------------------------------------------------------------------
#define CRC0DAT_CRC0DAT__FMASK 0xFF ///< CRC Data Output
#define CRC0DAT_CRC0DAT__SHIFT 0x00 ///< CRC Data Output
                                                        
//------------------------------------------------------------------------------
// CRC0FLIP Enums (CRC0 Bit Flip @ 0xCF)
//------------------------------------------------------------------------------
#define CRC0FLIP_CRC0FLIP__FMASK 0xFF ///< CRC0 Bit Flip
#define CRC0FLIP_CRC0FLIP__SHIFT 0x00 ///< CRC0 Bit Flip
                                                        
//------------------------------------------------------------------------------
// CRC0IN Enums (CRC0 Data Input @ 0xDD)
//------------------------------------------------------------------------------
#define CRC0IN_CRC0IN__FMASK 0xFF ///< CRC Data Input
#define CRC0IN_CRC0IN__SHIFT 0x00 ///< CRC Data Input
                                                     
//------------------------------------------------------------------------------
// DERIVID Enums (Derivative Identification @ 0xAD)
//------------------------------------------------------------------------------
#define DERIVID_DERIVID__FMASK              0xFF ///< Derivative ID         
#define DERIVID_DERIVID__SHIFT              0x00 ///< Derivative ID         
#define DERIVID_DERIVID__EFM8BB10F8G_QSOP24 0x01 ///< EFM8BB10F8G-{R}-QSOP24
#define DERIVID_DERIVID__EFM8BB10F8G_QFN20  0x02 ///< EFM8BB10F8G-{R}-QFN20 
#define DERIVID_DERIVID__EFM8BB10F8G_SOIC16 0x03 ///< EFM8BB10F8G-{R}-SOIC16
#define DERIVID_DERIVID__EFM8BB10F4G_QFN20  0x05 ///< EFM8BB10F4G-{R}-QFN20 
#define DERIVID_DERIVID__EFM8BB10F2G_QFN20  0x08 ///< EFM8BB10F2G-{R}-QFN20 
                                                                            
//------------------------------------------------------------------------------
// DEVICEID Enums (Device Identification @ 0xB5)
//------------------------------------------------------------------------------
#define DEVICEID_DEVICEID__FMASK 0xFF ///< Device ID
#define DEVICEID_DEVICEID__SHIFT 0x00 ///< Device ID
                                                    
//------------------------------------------------------------------------------
// REVID Enums (Revision Identifcation @ 0xB6)
//------------------------------------------------------------------------------
#define REVID_REVID__FMASK 0xFF ///< Revision ID
#define REVID_REVID__SHIFT 0x00 ///< Revision ID
#define REVID_REVID__REV_A 0x02 ///< Revision A 
                                                
//------------------------------------------------------------------------------
// IT01CF Enums (INT0/INT1 Configuration @ 0xE4)
//------------------------------------------------------------------------------
#define IT01CF_IN0SL__FMASK       0x07 ///< INT0 Port Pin Selection   
#define IT01CF_IN0SL__SHIFT       0x00 ///< INT0 Port Pin Selection   
#define IT01CF_IN0SL__P0_0        0x00 ///< Select P0.0.              
#define IT01CF_IN0SL__P0_1        0x01 ///< Select P0.1.              
#define IT01CF_IN0SL__P0_2        0x02 ///< Select P0.2.              
#define IT01CF_IN0SL__P0_3        0x03 ///< Select P0.3.              
#define IT01CF_IN0SL__P0_4        0x04 ///< Select P0.4.              
#define IT01CF_IN0SL__P0_5        0x05 ///< Select P0.5.              
#define IT01CF_IN0SL__P0_6        0x06 ///< Select P0.6.              
#define IT01CF_IN0SL__P0_7        0x07 ///< Select P0.7.              
                                                                      
#define IT01CF_IN0PL__BMASK       0x08 ///< INT0 Polarity             
#define IT01CF_IN0PL__SHIFT       0x03 ///< INT0 Polarity             
#define IT01CF_IN0PL__ACTIVE_LOW  0x00 ///< INT0 input is active low. 
#define IT01CF_IN0PL__ACTIVE_HIGH 0x08 ///< INT0 input is active high.
                                                                      
#define IT01CF_IN1SL__FMASK       0x70 ///< INT1 Port Pin Selection   
#define IT01CF_IN1SL__SHIFT       0x04 ///< INT1 Port Pin Selection   
#define IT01CF_IN1SL__P0_0        0x00 ///< Select P0.0.              
#define IT01CF_IN1SL__P0_1        0x10 ///< Select P0.1.              
#define IT01CF_IN1SL__P0_2        0x20 ///< Select P0.2.              
#define IT01CF_IN1SL__P0_3        0x30 ///< Select P0.3.              
#define IT01CF_IN1SL__P0_4        0x40 ///< Select P0.4.              
#define IT01CF_IN1SL__P0_5        0x50 ///< Select P0.5.              
#define IT01CF_IN1SL__P0_6        0x60 ///< Select P0.6.              
#define IT01CF_IN1SL__P0_7        0x70 ///< Select P0.7.              
                                                                      
#define IT01CF_IN1PL__BMASK       0x80 ///< INT1 Polarity             
#define IT01CF_IN1PL__SHIFT       0x07 ///< INT1 Polarity             
#define IT01CF_IN1PL__ACTIVE_LOW  0x00 ///< INT1 input is active low. 
#define IT01CF_IN1PL__ACTIVE_HIGH 0x80 ///< INT1 input is active high.
                                                                      
//------------------------------------------------------------------------------
// FLKEY Enums (Flash Lock and Key @ 0xB7)
//------------------------------------------------------------------------------
#define FLKEY_FLKEY__FMASK    0xFF ///< Flash Lock and Key                             
#define FLKEY_FLKEY__SHIFT    0x00 ///< Flash Lock and Key                             
#define FLKEY_FLKEY__LOCKED   0x00 ///< Flash is write/erase locked.                   
#define FLKEY_FLKEY__FIRST    0x01 ///< The first key code has been written (0xA5).    
#define FLKEY_FLKEY__UNLOCKED 0x02 ///< Flash is unlocked (writes/erases allowed).     
#define FLKEY_FLKEY__DISABLED 0x03 ///< Flash writes/erases are disabled until the next
                                   ///< reset.                                         
#define FLKEY_FLKEY__KEY1     0xA5 ///< Flash writes and erases are enabled by writing 
                                   ///< 0xA5 followed by 0xF1 to the FLKEY register.   
#define FLKEY_FLKEY__KEY2     0xF1 ///< Flash writes and erases are enabled by writing 
                                   ///< 0xA5 followed by 0xF1 to the FLKEY register.   
                                                                                       
//------------------------------------------------------------------------------
// PSCTL Enums (Program Store Control @ 0x8F)
//------------------------------------------------------------------------------
#define PSCTL_PSWE__BMASK          0x01 ///< Program Store Write Enable                      
#define PSCTL_PSWE__SHIFT          0x00 ///< Program Store Write Enable                      
#define PSCTL_PSWE__WRITE_DISABLED 0x00 ///< Writes to flash program memory disabled.        
#define PSCTL_PSWE__WRITE_ENABLED  0x01 ///< Writes to flash program memory enabled; the MOVX
                                        ///< write instruction targets flash memory.         
                                                                                             
#define PSCTL_PSEE__BMASK          0x02 ///< Program Store Erase Enable                      
#define PSCTL_PSEE__SHIFT          0x01 ///< Program Store Erase Enable                      
#define PSCTL_PSEE__ERASE_DISABLED 0x00 ///< Flash program memory erasure disabled.          
#define PSCTL_PSEE__ERASE_ENABLED  0x02 ///< Flash program memory erasure enabled.           
                                                                                             
//------------------------------------------------------------------------------
// HFO0CAL Enums (High Frequency Oscillator 0 Calibration @ 0xC7)
//------------------------------------------------------------------------------
#define HFO0CAL_HFO0CAL__FMASK 0xFF ///< Oscillator Calibration
#define HFO0CAL_HFO0CAL__SHIFT 0x00 ///< Oscillator Calibration
                                                               
//------------------------------------------------------------------------------
// EIE1 Enums (Extended Interrupt Enable 1 @ 0xE6)
//------------------------------------------------------------------------------
#define EIE1_ESMB0__BMASK     0x01 ///< SMBus (SMB0) Interrupt Enable                     
#define EIE1_ESMB0__SHIFT     0x00 ///< SMBus (SMB0) Interrupt Enable                     
#define EIE1_ESMB0__DISABLED  0x00 ///< Disable all SMB0 interrupts.                      
#define EIE1_ESMB0__ENABLED   0x01 ///< Enable interrupt requests generated by SMB0.      
                                                                                          
#define EIE1_EMAT__BMASK      0x02 ///< Port Match Interrupts Enable                      
#define EIE1_EMAT__SHIFT      0x01 ///< Port Match Interrupts Enable                      
#define EIE1_EMAT__DISABLED   0x00 ///< Disable all Port Match interrupts.                
#define EIE1_EMAT__ENABLED    0x02 ///< Enable interrupt requests generated by a Port     
                                   ///< Match.                                            
                                                                                          
#define EIE1_EWADC0__BMASK    0x04 ///< ADC0 Window Comparison Interrupt Enable           
#define EIE1_EWADC0__SHIFT    0x02 ///< ADC0 Window Comparison Interrupt Enable           
#define EIE1_EWADC0__DISABLED 0x00 ///< Disable ADC0 Window Comparison interrupt.         
#define EIE1_EWADC0__ENABLED  0x04 ///< Enable interrupt requests generated by ADC0 Window
                                   ///< Compare flag (ADWINT).                            
                                                                                          
#define EIE1_EADC0__BMASK     0x08 ///< ADC0 Conversion Complete Interrupt Enable         
#define EIE1_EADC0__SHIFT     0x03 ///< ADC0 Conversion Complete Interrupt Enable         
#define EIE1_EADC0__DISABLED  0x00 ///< Disable ADC0 Conversion Complete interrupt.       
#define EIE1_EADC0__ENABLED   0x08 ///< Enable interrupt requests generated by the ADINT  
                                   ///< flag.                                             
                                                                                          
#define EIE1_EPCA0__BMASK     0x10 ///< Programmable Counter Array (PCA0) Interrupt Enable
#define EIE1_EPCA0__SHIFT     0x04 ///< Programmable Counter Array (PCA0) Interrupt Enable
#define EIE1_EPCA0__DISABLED  0x00 ///< Disable all PCA0 interrupts.                      
#define EIE1_EPCA0__ENABLED   0x10 ///< Enable interrupt requests generated by PCA0.      
                                                                                          
#define EIE1_ECP0__BMASK      0x20 ///< Comparator0 (CP0) Interrupt Enable                
#define EIE1_ECP0__SHIFT      0x05 ///< Comparator0 (CP0) Interrupt Enable                
#define EIE1_ECP0__DISABLED   0x00 ///< Disable CP0 interrupts.                           
#define EIE1_ECP0__ENABLED    0x20 ///< Enable interrupt requests generated by the        
                                   ///< comparator 0 CPRIF or CPFIF flags.                
                                                                                          
#define EIE1_ECP1__BMASK      0x40 ///< Comparator1 (CP1) Interrupt Enable                
#define EIE1_ECP1__SHIFT      0x06 ///< Comparator1 (CP1) Interrupt Enable                
#define EIE1_ECP1__DISABLED   0x00 ///< Disable CP1 interrupts.                           
#define EIE1_ECP1__ENABLED    0x40 ///< Enable interrupt requests generated by the        
                                   ///< comparator 1 CPRIF or CPFIF flags.                
                                                                                          
#define EIE1_ET3__BMASK       0x80 ///< Timer 3 Interrupt Enable                          
#define EIE1_ET3__SHIFT       0x07 ///< Timer 3 Interrupt Enable                          
#define EIE1_ET3__DISABLED    0x00 ///< Disable Timer 3 interrupts.                       
#define EIE1_ET3__ENABLED     0x80 ///< Enable interrupt requests generated by the TF3L or
                                   ///< TF3H flags.                                       
                                                                                          
//------------------------------------------------------------------------------
// EIP1 Enums (Extended Interrupt Priority 1 @ 0xF3)
//------------------------------------------------------------------------------
#define EIP1_PSMB0__BMASK  0x01 ///< SMBus (SMB0) Interrupt Priority Control                     
#define EIP1_PSMB0__SHIFT  0x00 ///< SMBus (SMB0) Interrupt Priority Control                     
#define EIP1_PSMB0__LOW    0x00 ///< SMB0 interrupt set to low priority level.                   
#define EIP1_PSMB0__HIGH   0x01 ///< SMB0 interrupt set to high priority level.                  
                                                                                                 
#define EIP1_PMAT__BMASK   0x02 ///< Port Match Interrupt Priority Control                       
#define EIP1_PMAT__SHIFT   0x01 ///< Port Match Interrupt Priority Control                       
#define EIP1_PMAT__LOW     0x00 ///< Port Match interrupt set to low priority level.             
#define EIP1_PMAT__HIGH    0x02 ///< Port Match interrupt set to high priority level.            
                                                                                                 
#define EIP1_PWADC0__BMASK 0x04 ///< ADC0 Window Comparator Interrupt Priority Control           
#define EIP1_PWADC0__SHIFT 0x02 ///< ADC0 Window Comparator Interrupt Priority Control           
#define EIP1_PWADC0__LOW   0x00 ///< ADC0 Window interrupt set to low priority level.            
#define EIP1_PWADC0__HIGH  0x04 ///< ADC0 Window interrupt set to high priority level.           
                                                                                                 
#define EIP1_PADC0__BMASK  0x08 ///< ADC0 Conversion Complete Interrupt Priority Control         
#define EIP1_PADC0__SHIFT  0x03 ///< ADC0 Conversion Complete Interrupt Priority Control         
#define EIP1_PADC0__LOW    0x00 ///< ADC0 Conversion Complete interrupt set to low               
                                ///< priority level.                                             
#define EIP1_PADC0__HIGH   0x08 ///< ADC0 Conversion Complete interrupt set to high              
                                ///< priority level.                                             
                                                                                                 
#define EIP1_PPCA0__BMASK  0x10 ///< Programmable Counter Array (PCA0) Interrupt Priority Control
#define EIP1_PPCA0__SHIFT  0x04 ///< Programmable Counter Array (PCA0) Interrupt Priority Control
#define EIP1_PPCA0__LOW    0x00 ///< PCA0 interrupt set to low priority level.                   
#define EIP1_PPCA0__HIGH   0x10 ///< PCA0 interrupt set to high priority level.                  
                                                                                                 
#define EIP1_PCP0__BMASK   0x20 ///< Comparator0 (CP0) Interrupt Priority Control                
#define EIP1_PCP0__SHIFT   0x05 ///< Comparator0 (CP0) Interrupt Priority Control                
#define EIP1_PCP0__LOW     0x00 ///< CP0 interrupt set to low priority level.                    
#define EIP1_PCP0__HIGH    0x20 ///< CP0 interrupt set to high priority level.                   
                                                                                                 
#define EIP1_PCP1__BMASK   0x40 ///< Comparator1 (CP1) Interrupt Priority Control                
#define EIP1_PCP1__SHIFT   0x06 ///< Comparator1 (CP1) Interrupt Priority Control                
#define EIP1_PCP1__LOW     0x00 ///< CP1 interrupt set to low priority level.                    
#define EIP1_PCP1__HIGH    0x40 ///< CP1 interrupt set to high priority level.                   
                                                                                                 
#define EIP1_PT3__BMASK    0x80 ///< Timer 3 Interrupt Priority Control                          
#define EIP1_PT3__SHIFT    0x07 ///< Timer 3 Interrupt Priority Control                          
#define EIP1_PT3__LOW      0x00 ///< Timer 3 interrupts set to low priority level.               
#define EIP1_PT3__HIGH     0x80 ///< Timer 3 interrupts set to high priority level.              
                                                                                                 
//------------------------------------------------------------------------------
// IE Enums (Interrupt Enable @ 0xA8)
//------------------------------------------------------------------------------
#define IE_EX0__BMASK      0x01 ///< External Interrupt 0 Enable                       
#define IE_EX0__SHIFT      0x00 ///< External Interrupt 0 Enable                       
#define IE_EX0__DISABLED   0x00 ///< Disable external interrupt 0.                     
#define IE_EX0__ENABLED    0x01 ///< Enable interrupt requests generated by the INT0   
                                ///< input.                                            
                                                                                       
#define IE_ET0__BMASK      0x02 ///< Timer 0 Interrupt Enable                          
#define IE_ET0__SHIFT      0x01 ///< Timer 0 Interrupt Enable                          
#define IE_ET0__DISABLED   0x00 ///< Disable all Timer 0 interrupt.                    
#define IE_ET0__ENABLED    0x02 ///< Enable interrupt requests generated by the TF0    
                                ///< flag.                                             
                                                                                       
#define IE_EX1__BMASK      0x04 ///< External Interrupt 1 Enable                       
#define IE_EX1__SHIFT      0x02 ///< External Interrupt 1 Enable                       
#define IE_EX1__DISABLED   0x00 ///< Disable external interrupt 1.                     
#define IE_EX1__ENABLED    0x04 ///< Enable interrupt requests generated by the INT1   
                                ///< input.                                            
                                                                                       
#define IE_ET1__BMASK      0x08 ///< Timer 1 Interrupt Enable                          
#define IE_ET1__SHIFT      0x03 ///< Timer 1 Interrupt Enable                          
#define IE_ET1__DISABLED   0x00 ///< Disable all Timer 1 interrupt.                    
#define IE_ET1__ENABLED    0x08 ///< Enable interrupt requests generated by the TF1    
                                ///< flag.                                             
                                                                                       
#define IE_ES0__BMASK      0x10 ///< UART0 Interrupt Enable                            
#define IE_ES0__SHIFT      0x04 ///< UART0 Interrupt Enable                            
#define IE_ES0__DISABLED   0x00 ///< Disable UART0 interrupt.                          
#define IE_ES0__ENABLED    0x10 ///< Enable UART0 interrupt.                           
                                                                                       
#define IE_ET2__BMASK      0x20 ///< Timer 2 Interrupt Enable                          
#define IE_ET2__SHIFT      0x05 ///< Timer 2 Interrupt Enable                          
#define IE_ET2__DISABLED   0x00 ///< Disable Timer 2 interrupt.                        
#define IE_ET2__ENABLED    0x20 ///< Enable interrupt requests generated by the TF2L or
                                ///< TF2H flags.                                       
                                                                                       
#define IE_ESPI0__BMASK    0x40 ///< SPI0 Interrupt Enable                             
#define IE_ESPI0__SHIFT    0x06 ///< SPI0 Interrupt Enable                             
#define IE_ESPI0__DISABLED 0x00 ///< Disable all SPI0 interrupts.                      
#define IE_ESPI0__ENABLED  0x40 ///< Enable interrupt requests generated by SPI0.      
                                                                                       
#define IE_EA__BMASK       0x80 ///< All Interrupts Enable                             
#define IE_EA__SHIFT       0x07 ///< All Interrupts Enable                             
#define IE_EA__DISABLED    0x00 ///< Disable all interrupt sources.                    
#define IE_EA__ENABLED     0x80 ///< Enable each interrupt according to its individual 
                                ///< mask setting.                                     
                                                                                       
//------------------------------------------------------------------------------
// IP Enums (Interrupt Priority @ 0xB8)
//------------------------------------------------------------------------------
#define IP_PX0__BMASK   0x01 ///< External Interrupt 0 Priority Control                        
#define IP_PX0__SHIFT   0x00 ///< External Interrupt 0 Priority Control                        
#define IP_PX0__LOW     0x00 ///< External Interrupt 0 set to low priority level.              
#define IP_PX0__HIGH    0x01 ///< External Interrupt 0 set to high priority level.             
                                                                                               
#define IP_PT0__BMASK   0x02 ///< Timer 0 Interrupt Priority Control                           
#define IP_PT0__SHIFT   0x01 ///< Timer 0 Interrupt Priority Control                           
#define IP_PT0__LOW     0x00 ///< Timer 0 interrupt set to low priority level.                 
#define IP_PT0__HIGH    0x02 ///< Timer 0 interrupt set to high priority level.                
                                                                                               
#define IP_PX1__BMASK   0x04 ///< External Interrupt 1 Priority Control                        
#define IP_PX1__SHIFT   0x02 ///< External Interrupt 1 Priority Control                        
#define IP_PX1__LOW     0x00 ///< External Interrupt 1 set to low priority level.              
#define IP_PX1__HIGH    0x04 ///< External Interrupt 1 set to high priority level.             
                                                                                               
#define IP_PT1__BMASK   0x08 ///< Timer 1 Interrupt Priority Control                           
#define IP_PT1__SHIFT   0x03 ///< Timer 1 Interrupt Priority Control                           
#define IP_PT1__LOW     0x00 ///< Timer 1 interrupt set to low priority level.                 
#define IP_PT1__HIGH    0x08 ///< Timer 1 interrupt set to high priority level.                
                                                                                               
#define IP_PS0__BMASK   0x10 ///< UART0 Interrupt Priority Control                             
#define IP_PS0__SHIFT   0x04 ///< UART0 Interrupt Priority Control                             
#define IP_PS0__LOW     0x00 ///< UART0 interrupt set to low priority level.                   
#define IP_PS0__HIGH    0x10 ///< UART0 interrupt set to high priority level.                  
                                                                                               
#define IP_PT2__BMASK   0x20 ///< Timer 2 Interrupt Priority Control                           
#define IP_PT2__SHIFT   0x05 ///< Timer 2 Interrupt Priority Control                           
#define IP_PT2__LOW     0x00 ///< Timer 2 interrupt set to low priority level.                 
#define IP_PT2__HIGH    0x20 ///< Timer 2 interrupt set to high priority level.                
                                                                                               
#define IP_PSPI0__BMASK 0x40 ///< Serial Peripheral Interface (SPI0) Interrupt Priority Control
#define IP_PSPI0__SHIFT 0x06 ///< Serial Peripheral Interface (SPI0) Interrupt Priority Control
#define IP_PSPI0__LOW   0x00 ///< SPI0 interrupt set to low priority level.                    
#define IP_PSPI0__HIGH  0x40 ///< SPI0 interrupt set to high priority level.                   
                                                                                               
//------------------------------------------------------------------------------
// LFO0CN Enums (Low Frequency Oscillator Control @ 0xB1)
//------------------------------------------------------------------------------
#define LFO0CN_OSCLD__FMASK       0x03 ///< Internal L-F Oscillator Divider Select           
#define LFO0CN_OSCLD__SHIFT       0x00 ///< Internal L-F Oscillator Divider Select           
#define LFO0CN_OSCLD__DIVIDE_BY_8 0x00 ///< Divide by 8 selected.                            
#define LFO0CN_OSCLD__DIVIDE_BY_4 0x01 ///< Divide by 4 selected.                            
#define LFO0CN_OSCLD__DIVIDE_BY_2 0x02 ///< Divide by 2 selected.                            
#define LFO0CN_OSCLD__DIVIDE_BY_1 0x03 ///< Divide by 1 selected.                            
                                                                                             
#define LFO0CN_OSCLF__FMASK       0x3C ///< Internal L-F Oscillator Frequency Control        
#define LFO0CN_OSCLF__SHIFT       0x02 ///< Internal L-F Oscillator Frequency Control        
                                                                                             
#define LFO0CN_OSCLRDY__BMASK     0x40 ///< Internal L-F Oscillator Ready                    
#define LFO0CN_OSCLRDY__SHIFT     0x06 ///< Internal L-F Oscillator Ready                    
#define LFO0CN_OSCLRDY__NOT_SET   0x00 ///< Internal L-F Oscillator frequency not stabilized.
#define LFO0CN_OSCLRDY__SET       0x40 ///< Internal L-F Oscillator frequency stabilized.    
                                                                                             
#define LFO0CN_OSCLEN__BMASK      0x80 ///< Internal L-F Oscillator Enable                   
#define LFO0CN_OSCLEN__SHIFT      0x07 ///< Internal L-F Oscillator Enable                   
#define LFO0CN_OSCLEN__DISABLED   0x00 ///< Internal L-F Oscillator Disabled.                
#define LFO0CN_OSCLEN__ENABLED    0x80 ///< Internal L-F Oscillator Enabled.                 
                                                                                             
//------------------------------------------------------------------------------
// PRTDRV Enums (Port Drive Strength @ 0xF6)
//------------------------------------------------------------------------------
#define PRTDRV_P0DRV__BMASK      0x01 ///< Port 0 Drive Strength                  
#define PRTDRV_P0DRV__SHIFT      0x00 ///< Port 0 Drive Strength                  
#define PRTDRV_P0DRV__LOW_DRIVE  0x00 ///< All pins on P0 use low drive strength. 
#define PRTDRV_P0DRV__HIGH_DRIVE 0x01 ///< All pins on P0 use high drive strength.
                                                                                  
#define PRTDRV_P1DRV__BMASK      0x02 ///< Port 1 Drive Strength                  
#define PRTDRV_P1DRV__SHIFT      0x01 ///< Port 1 Drive Strength                  
#define PRTDRV_P1DRV__LOW_DRIVE  0x00 ///< All pins on P1 use low drive strength. 
#define PRTDRV_P1DRV__HIGH_DRIVE 0x02 ///< All pins on P1 use high drive strength.
                                                                                  
#define PRTDRV_P2DRV__BMASK      0x04 ///< Port 2 Drive Strength                  
#define PRTDRV_P2DRV__SHIFT      0x02 ///< Port 2 Drive Strength                  
#define PRTDRV_P2DRV__LOW_DRIVE  0x00 ///< All pins on P2 use low drive strength. 
#define PRTDRV_P2DRV__HIGH_DRIVE 0x04 ///< All pins on P2 use high drive strength.
                                                                                  
//------------------------------------------------------------------------------
// XBR0 Enums (Port I/O Crossbar 0 @ 0xE1)
//------------------------------------------------------------------------------
#define XBR0_URT0E__BMASK     0x01 ///< UART I/O Output Enable                        
#define XBR0_URT0E__SHIFT     0x00 ///< UART I/O Output Enable                        
#define XBR0_URT0E__DISABLED  0x00 ///< UART I/O unavailable at Port pin.             
#define XBR0_URT0E__ENABLED   0x01 ///< UART TX, RX routed to Port pins P0.4 and P0.5.
                                                                                      
#define XBR0_SPI0E__BMASK     0x02 ///< SPI I/O Enable                                
#define XBR0_SPI0E__SHIFT     0x01 ///< SPI I/O Enable                                
#define XBR0_SPI0E__DISABLED  0x00 ///< SPI I/O unavailable at Port pins.             
#define XBR0_SPI0E__ENABLED   0x02 ///< SPI I/O routed to Port pins. The SPI can be   
                                   ///< assigned either 3 or 4 GPIO pins.             
                                                                                      
#define XBR0_SMB0E__BMASK     0x04 ///< SMB0 I/O Enable                               
#define XBR0_SMB0E__SHIFT     0x02 ///< SMB0 I/O Enable                               
#define XBR0_SMB0E__DISABLED  0x00 ///< SMBus 0 I/O unavailable at Port pins.         
#define XBR0_SMB0E__ENABLED   0x04 ///< SMBus 0 I/O routed to Port pins.              
                                                                                      
#define XBR0_CP0E__BMASK      0x08 ///< Comparator0 Output Enable                     
#define XBR0_CP0E__SHIFT      0x03 ///< Comparator0 Output Enable                     
#define XBR0_CP0E__DISABLED   0x00 ///< CP0 unavailable at Port pin.                  
#define XBR0_CP0E__ENABLED    0x08 ///< CP0 routed to Port pin.                       
                                                                                      
#define XBR0_CP0AE__BMASK     0x10 ///< Comparator0 Asynchronous Output Enable        
#define XBR0_CP0AE__SHIFT     0x04 ///< Comparator0 Asynchronous Output Enable        
#define XBR0_CP0AE__DISABLED  0x00 ///< Asynchronous CP0 unavailable at Port pin.     
#define XBR0_CP0AE__ENABLED   0x10 ///< Asynchronous CP0 routed to Port pin.          
                                                                                      
#define XBR0_CP1E__BMASK      0x20 ///< Comparator1 Output Enable                     
#define XBR0_CP1E__SHIFT      0x05 ///< Comparator1 Output Enable                     
#define XBR0_CP1E__DISABLED   0x00 ///< CP1 unavailable at Port pin.                  
#define XBR0_CP1E__ENABLED    0x20 ///< CP1 routed to Port pin.                       
                                                                                      
#define XBR0_CP1AE__BMASK     0x40 ///< Comparator1 Asynchronous Output Enable        
#define XBR0_CP1AE__SHIFT     0x06 ///< Comparator1 Asynchronous Output Enable        
#define XBR0_CP1AE__DISABLED  0x00 ///< Asynchronous CP1 unavailable at Port pin.     
#define XBR0_CP1AE__ENABLED   0x40 ///< Asynchronous CP1 routed to Port pin.          
                                                                                      
#define XBR0_SYSCKE__BMASK    0x80 ///< SYSCLK Output Enable                          
#define XBR0_SYSCKE__SHIFT    0x07 ///< SYSCLK Output Enable                          
#define XBR0_SYSCKE__DISABLED 0x00 ///< SYSCLK unavailable at Port pin.               
#define XBR0_SYSCKE__ENABLED  0x80 ///< SYSCLK output routed to Port pin.             
                                                                                      
//------------------------------------------------------------------------------
// XBR1 Enums (Port I/O Crossbar 1 @ 0xE2)
//------------------------------------------------------------------------------
#define XBR1_PCA0ME__FMASK          0x03 ///< PCA Module I/O Enable                
#define XBR1_PCA0ME__SHIFT          0x00 ///< PCA Module I/O Enable                
#define XBR1_PCA0ME__DISABLED       0x00 ///< All PCA I/O unavailable at Port pins.
#define XBR1_PCA0ME__CEX0           0x01 ///< CEX0 routed to Port pin.             
#define XBR1_PCA0ME__CEX0_CEX1      0x02 ///< CEX0, CEX1 routed to Port pins.      
#define XBR1_PCA0ME__CEX0_CEX1_CEX2 0x03 ///< CEX0, CEX1, CEX2 routed to Port pins.
                                                                                   
#define XBR1_ECIE__BMASK            0x04 ///< PCA0 External Counter Input Enable   
#define XBR1_ECIE__SHIFT            0x02 ///< PCA0 External Counter Input Enable   
#define XBR1_ECIE__DISABLED         0x00 ///< ECI unavailable at Port pin.         
#define XBR1_ECIE__ENABLED          0x04 ///< ECI routed to Port pin.              
                                                                                   
#define XBR1_T0E__BMASK             0x08 ///< T0 Enable                            
#define XBR1_T0E__SHIFT             0x03 ///< T0 Enable                            
#define XBR1_T0E__DISABLED          0x00 ///< T0 unavailable at Port pin.          
#define XBR1_T0E__ENABLED           0x08 ///< T0 routed to Port pin.               
                                                                                   
#define XBR1_T1E__BMASK             0x10 ///< T1 Enable                            
#define XBR1_T1E__SHIFT             0x04 ///< T1 Enable                            
#define XBR1_T1E__DISABLED          0x00 ///< T1 unavailable at Port pin.          
#define XBR1_T1E__ENABLED           0x10 ///< T1 routed to Port pin.               
                                                                                   
#define XBR1_T2E__BMASK             0x20 ///< T2 Enable                            
#define XBR1_T2E__SHIFT             0x05 ///< T2 Enable                            
#define XBR1_T2E__DISABLED          0x00 ///< T2 unavailable at Port pin.          
#define XBR1_T2E__ENABLED           0x20 ///< T2 routed to Port pin.               
                                                                                   
//------------------------------------------------------------------------------
// XBR2 Enums (Port I/O Crossbar 2 @ 0xE3)
//------------------------------------------------------------------------------
#define XBR2_XBARE__BMASK               0x40 ///< Crossbar Enable                                 
#define XBR2_XBARE__SHIFT               0x06 ///< Crossbar Enable                                 
#define XBR2_XBARE__DISABLED            0x00 ///< Crossbar disabled.                              
#define XBR2_XBARE__ENABLED             0x40 ///< Crossbar enabled.                               
                                                                                                  
#define XBR2_WEAKPUD__BMASK             0x80 ///< Port I/O Weak Pullup Disable                    
#define XBR2_WEAKPUD__SHIFT             0x07 ///< Port I/O Weak Pullup Disable                    
#define XBR2_WEAKPUD__PULL_UPS_ENABLED  0x00 ///< Weak Pullups enabled (except for Ports whose I/O
                                             ///< are configured for analog mode).                
#define XBR2_WEAKPUD__PULL_UPS_DISABLED 0x80 ///< Weak Pullups disabled.                          
                                                                                                  
//------------------------------------------------------------------------------
// PCA0CPH0 Enums (PCA Channel 0 Capture Module High Byte @ 0xFC)
//------------------------------------------------------------------------------
#define PCA0CPH0_PCA0CPH0__FMASK 0xFF ///< PCA Channel 0 Capture Module High Byte
#define PCA0CPH0_PCA0CPH0__SHIFT 0x00 ///< PCA Channel 0 Capture Module High Byte
                                                                                 
//------------------------------------------------------------------------------
// PCA0CPL0 Enums (PCA Channel 0 Capture Module Low Byte @ 0xFB)
//------------------------------------------------------------------------------
#define PCA0CPL0_PCA0CPL0__FMASK 0xFF ///< PCA Channel 0 Capture Module Low Byte
#define PCA0CPL0_PCA0CPL0__SHIFT 0x00 ///< PCA Channel 0 Capture Module Low Byte
                                                                                
//------------------------------------------------------------------------------
// PCA0CPM0 Enums (PCA Channel 0 Capture/Compare Mode @ 0xDA)
//------------------------------------------------------------------------------
#define PCA0CPM0_ECCF__BMASK    0x01 ///< Channel 0 Capture/Compare Flag Interrupt Enable
#define PCA0CPM0_ECCF__SHIFT    0x00 ///< Channel 0 Capture/Compare Flag Interrupt Enable
#define PCA0CPM0_ECCF__DISABLED 0x00 ///< Disable CCF0 interrupts.                       
#define PCA0CPM0_ECCF__ENABLED  0x01 ///< Enable a Capture/Compare Flag interrupt request
                                     ///< when CCF0 is set.                              
                                                                                         
#define PCA0CPM0_PWM__BMASK     0x02 ///< Channel 0 Pulse Width Modulation Mode Enable   
#define PCA0CPM0_PWM__SHIFT     0x01 ///< Channel 0 Pulse Width Modulation Mode Enable   
#define PCA0CPM0_PWM__DISABLED  0x00 ///< Disable PWM function.                          
#define PCA0CPM0_PWM__ENABLED   0x02 ///< Enable PWM function.                           
                                                                                         
#define PCA0CPM0_TOG__BMASK     0x04 ///< Channel 0 Toggle Function Enable               
#define PCA0CPM0_TOG__SHIFT     0x02 ///< Channel 0 Toggle Function Enable               
#define PCA0CPM0_TOG__DISABLED  0x00 ///< Disable toggle function.                       
#define PCA0CPM0_TOG__ENABLED   0x04 ///< Enable toggle function.                        
                                                                                         
#define PCA0CPM0_MAT__BMASK     0x08 ///< Channel 0 Match Function Enable                
#define PCA0CPM0_MAT__SHIFT     0x03 ///< Channel 0 Match Function Enable                
#define PCA0CPM0_MAT__DISABLED  0x00 ///< Disable match function.                        
#define PCA0CPM0_MAT__ENABLED   0x08 ///< Enable match function.                         
                                                                                         
#define PCA0CPM0_CAPN__BMASK    0x10 ///< Channel 0 Capture Negative Function Enable     
#define PCA0CPM0_CAPN__SHIFT    0x04 ///< Channel 0 Capture Negative Function Enable     
#define PCA0CPM0_CAPN__DISABLED 0x00 ///< Disable negative edge capture.                 
#define PCA0CPM0_CAPN__ENABLED  0x10 ///< Enable negative edge capture.                  
                                                                                         
#define PCA0CPM0_CAPP__BMASK    0x20 ///< Channel 0 Capture Positive Function Enable     
#define PCA0CPM0_CAPP__SHIFT    0x05 ///< Channel 0 Capture Positive Function Enable     
#define PCA0CPM0_CAPP__DISABLED 0x00 ///< Disable positive edge capture.                 
#define PCA0CPM0_CAPP__ENABLED  0x20 ///< Enable positive edge capture.                  
                                                                                         
#define PCA0CPM0_ECOM__BMASK    0x40 ///< Channel 0 Comparator Function Enable           
#define PCA0CPM0_ECOM__SHIFT    0x06 ///< Channel 0 Comparator Function Enable           
#define PCA0CPM0_ECOM__DISABLED 0x00 ///< Disable comparator function.                   
#define PCA0CPM0_ECOM__ENABLED  0x40 ///< Enable comparator function.                    
                                                                                         
#define PCA0CPM0_PWM16__BMASK   0x80 ///< Channel 0 16-bit Pulse Width Modulation Enable 
#define PCA0CPM0_PWM16__SHIFT   0x07 ///< Channel 0 16-bit Pulse Width Modulation Enable 
#define PCA0CPM0_PWM16__8_BIT   0x00 ///< 8 to 11-bit PWM selected.                      
#define PCA0CPM0_PWM16__16_BIT  0x80 ///< 16-bit PWM selected.                           
                                                                                         
//------------------------------------------------------------------------------
// PCA0CPH1 Enums (PCA Channel 1 Capture Module High Byte @ 0xEA)
//------------------------------------------------------------------------------
#define PCA0CPH1_PCA0CPH1__FMASK 0xFF ///< PCA Channel 1 Capture Module High Byte
#define PCA0CPH1_PCA0CPH1__SHIFT 0x00 ///< PCA Channel 1 Capture Module High Byte
                                                                                 
//------------------------------------------------------------------------------
// PCA0CPL1 Enums (PCA Channel 1 Capture Module Low Byte @ 0xE9)
//------------------------------------------------------------------------------
#define PCA0CPL1_PCA0CPL1__FMASK 0xFF ///< PCA Channel 1 Capture Module Low Byte
#define PCA0CPL1_PCA0CPL1__SHIFT 0x00 ///< PCA Channel 1 Capture Module Low Byte
                                                                                
//------------------------------------------------------------------------------
// PCA0CPM1 Enums (PCA Channel 1 Capture/Compare Mode @ 0xDB)
//------------------------------------------------------------------------------
#define PCA0CPM1_ECCF__BMASK    0x01 ///< Channel 1 Capture/Compare Flag Interrupt Enable
#define PCA0CPM1_ECCF__SHIFT    0x00 ///< Channel 1 Capture/Compare Flag Interrupt Enable
#define PCA0CPM1_ECCF__DISABLED 0x00 ///< Disable CCF1 interrupts.                       
#define PCA0CPM1_ECCF__ENABLED  0x01 ///< Enable a Capture/Compare Flag interrupt request
                                     ///< when CCF1 is set.                              
                                                                                         
#define PCA0CPM1_PWM__BMASK     0x02 ///< Channel 1 Pulse Width Modulation Mode Enable   
#define PCA0CPM1_PWM__SHIFT     0x01 ///< Channel 1 Pulse Width Modulation Mode Enable   
#define PCA0CPM1_PWM__DISABLED  0x00 ///< Disable PWM function.                          
#define PCA0CPM1_PWM__ENABLED   0x02 ///< Enable PWM function.                           
                                                                                         
#define PCA0CPM1_TOG__BMASK     0x04 ///< Channel 1 Toggle Function Enable               
#define PCA0CPM1_TOG__SHIFT     0x02 ///< Channel 1 Toggle Function Enable               
#define PCA0CPM1_TOG__DISABLED  0x00 ///< Disable toggle function.                       
#define PCA0CPM1_TOG__ENABLED   0x04 ///< Enable toggle function.                        
                                                                                         
#define PCA0CPM1_MAT__BMASK     0x08 ///< Channel 1 Match Function Enable                
#define PCA0CPM1_MAT__SHIFT     0x03 ///< Channel 1 Match Function Enable                
#define PCA0CPM1_MAT__DISABLED  0x00 ///< Disable match function.                        
#define PCA0CPM1_MAT__ENABLED   0x08 ///< Enable match function.                         
                                                                                         
#define PCA0CPM1_CAPN__BMASK    0x10 ///< Channel 1 Capture Negative Function Enable     
#define PCA0CPM1_CAPN__SHIFT    0x04 ///< Channel 1 Capture Negative Function Enable     
#define PCA0CPM1_CAPN__DISABLED 0x00 ///< Disable negative edge capture.                 
#define PCA0CPM1_CAPN__ENABLED  0x10 ///< Enable negative edge capture.                  
                                                                                         
#define PCA0CPM1_CAPP__BMASK    0x20 ///< Channel 1 Capture Positive Function Enable     
#define PCA0CPM1_CAPP__SHIFT    0x05 ///< Channel 1 Capture Positive Function Enable     
#define PCA0CPM1_CAPP__DISABLED 0x00 ///< Disable positive edge capture.                 
#define PCA0CPM1_CAPP__ENABLED  0x20 ///< Enable positive edge capture.                  
                                                                                         
#define PCA0CPM1_ECOM__BMASK    0x40 ///< Channel 1 Comparator Function Enable           
#define PCA0CPM1_ECOM__SHIFT    0x06 ///< Channel 1 Comparator Function Enable           
#define PCA0CPM1_ECOM__DISABLED 0x00 ///< Disable comparator function.                   
#define PCA0CPM1_ECOM__ENABLED  0x40 ///< Enable comparator function.                    
                                                                                         
#define PCA0CPM1_PWM16__BMASK   0x80 ///< Channel 1 16-bit Pulse Width Modulation Enable 
#define PCA0CPM1_PWM16__SHIFT   0x07 ///< Channel 1 16-bit Pulse Width Modulation Enable 
#define PCA0CPM1_PWM16__8_BIT   0x00 ///< 8 to 11-bit PWM selected.                      
#define PCA0CPM1_PWM16__16_BIT  0x80 ///< 16-bit PWM selected.                           
                                                                                         
//------------------------------------------------------------------------------
// PCA0CPH2 Enums (PCA Channel 2 Capture Module High Byte @ 0xEC)
//------------------------------------------------------------------------------
#define PCA0CPH2_PCA0CPH2__FMASK 0xFF ///< PCA Channel 2 Capture Module High Byte
#define PCA0CPH2_PCA0CPH2__SHIFT 0x00 ///< PCA Channel 2 Capture Module High Byte
                                                                                 
//------------------------------------------------------------------------------
// PCA0CPL2 Enums (PCA Channel 2 Capture Module Low Byte @ 0xEB)
//------------------------------------------------------------------------------
#define PCA0CPL2_PCA0CPL2__FMASK 0xFF ///< PCA Channel 2 Capture Module Low Byte
#define PCA0CPL2_PCA0CPL2__SHIFT 0x00 ///< PCA Channel 2 Capture Module Low Byte
                                                                                
//------------------------------------------------------------------------------
// PCA0CPM2 Enums (PCA Channel 2 Capture/Compare Mode @ 0xDC)
//------------------------------------------------------------------------------
#define PCA0CPM2_ECCF__BMASK    0x01 ///< Channel 2 Capture/Compare Flag Interrupt Enable
#define PCA0CPM2_ECCF__SHIFT    0x00 ///< Channel 2 Capture/Compare Flag Interrupt Enable
#define PCA0CPM2_ECCF__DISABLED 0x00 ///< Disable CCF2 interrupts.                       
#define PCA0CPM2_ECCF__ENABLED  0x01 ///< Enable a Capture/Compare Flag interrupt request
                                     ///< when CCF2 is set.                              
                                                                                         
#define PCA0CPM2_PWM__BMASK     0x02 ///< Channel 2 Pulse Width Modulation Mode Enable   
#define PCA0CPM2_PWM__SHIFT     0x01 ///< Channel 2 Pulse Width Modulation Mode Enable   
#define PCA0CPM2_PWM__DISABLED  0x00 ///< Disable PWM function.                          
#define PCA0CPM2_PWM__ENABLED   0x02 ///< Enable PWM function.                           
                                                                                         
#define PCA0CPM2_TOG__BMASK     0x04 ///< Channel 2 Toggle Function Enable               
#define PCA0CPM2_TOG__SHIFT     0x02 ///< Channel 2 Toggle Function Enable               
#define PCA0CPM2_TOG__DISABLED  0x00 ///< Disable toggle function.                       
#define PCA0CPM2_TOG__ENABLED   0x04 ///< Enable toggle function.                        
                                                                                         
#define PCA0CPM2_MAT__BMASK     0x08 ///< Channel 2 Match Function Enable                
#define PCA0CPM2_MAT__SHIFT     0x03 ///< Channel 2 Match Function Enable                
#define PCA0CPM2_MAT__DISABLED  0x00 ///< Disable match function.                        
#define PCA0CPM2_MAT__ENABLED   0x08 ///< Enable match function.                         
                                                                                         
#define PCA0CPM2_CAPN__BMASK    0x10 ///< Channel 2 Capture Negative Function Enable     
#define PCA0CPM2_CAPN__SHIFT    0x04 ///< Channel 2 Capture Negative Function Enable     
#define PCA0CPM2_CAPN__DISABLED 0x00 ///< Disable negative edge capture.                 
#define PCA0CPM2_CAPN__ENABLED  0x10 ///< Enable negative edge capture.                  
                                                                                         
#define PCA0CPM2_CAPP__BMASK    0x20 ///< Channel 2 Capture Positive Function Enable     
#define PCA0CPM2_CAPP__SHIFT    0x05 ///< Channel 2 Capture Positive Function Enable     
#define PCA0CPM2_CAPP__DISABLED 0x00 ///< Disable positive edge capture.                 
#define PCA0CPM2_CAPP__ENABLED  0x20 ///< Enable positive edge capture.                  
                                                                                         
#define PCA0CPM2_ECOM__BMASK    0x40 ///< Channel 2 Comparator Function Enable           
#define PCA0CPM2_ECOM__SHIFT    0x06 ///< Channel 2 Comparator Function Enable           
#define PCA0CPM2_ECOM__DISABLED 0x00 ///< Disable comparator function.                   
#define PCA0CPM2_ECOM__ENABLED  0x40 ///< Enable comparator function.                    
                                                                                         
#define PCA0CPM2_PWM16__BMASK   0x80 ///< Channel 2 16-bit Pulse Width Modulation Enable 
#define PCA0CPM2_PWM16__SHIFT   0x07 ///< Channel 2 16-bit Pulse Width Modulation Enable 
#define PCA0CPM2_PWM16__8_BIT   0x00 ///< 8 to 11-bit PWM selected.                      
#define PCA0CPM2_PWM16__16_BIT  0x80 ///< 16-bit PWM selected.                           
                                                                                         
//------------------------------------------------------------------------------
// PCA0CENT Enums (PCA Center Alignment Enable @ 0x9E)
//------------------------------------------------------------------------------
#define PCA0CENT_CEX0CEN__BMASK  0x01 ///< CEX0 Center Alignment Enable
#define PCA0CENT_CEX0CEN__SHIFT  0x00 ///< CEX0 Center Alignment Enable
#define PCA0CENT_CEX0CEN__EDGE   0x00 ///< Edge-aligned.               
#define PCA0CENT_CEX0CEN__CENTER 0x01 ///< Center-aligned.             
                                                                       
#define PCA0CENT_CEX1CEN__BMASK  0x02 ///< CEX1 Center Alignment Enable
#define PCA0CENT_CEX1CEN__SHIFT  0x01 ///< CEX1 Center Alignment Enable
#define PCA0CENT_CEX1CEN__EDGE   0x00 ///< Edge-aligned.               
#define PCA0CENT_CEX1CEN__CENTER 0x02 ///< Center-aligned.             
                                                                       
#define PCA0CENT_CEX2CEN__BMASK  0x04 ///< CEX2 Center Alignment Enable
#define PCA0CENT_CEX2CEN__SHIFT  0x02 ///< CEX2 Center Alignment Enable
#define PCA0CENT_CEX2CEN__EDGE   0x00 ///< Edge-aligned.               
#define PCA0CENT_CEX2CEN__CENTER 0x04 ///< Center-aligned.             
                                                                       
//------------------------------------------------------------------------------
// PCA0CLR Enums (PCA Comparator Clear Control @ 0x9C)
//------------------------------------------------------------------------------
#define PCA0CLR_CPCE0__BMASK    0x01 ///< Comparator Clear Enable for CEX0              
#define PCA0CLR_CPCE0__SHIFT    0x00 ///< Comparator Clear Enable for CEX0              
#define PCA0CLR_CPCE0__DISABLED 0x00 ///< Disable the comparator clear function on PCA  
                                     ///< channel 0.                                    
#define PCA0CLR_CPCE0__ENABLED  0x01 ///< Enable the comparator clear function on PCA   
                                     ///< channel 0.                                    
                                                                                        
#define PCA0CLR_CPCE1__BMASK    0x02 ///< Comparator Clear Enable for CEX1              
#define PCA0CLR_CPCE1__SHIFT    0x01 ///< Comparator Clear Enable for CEX1              
#define PCA0CLR_CPCE1__DISABLED 0x00 ///< Disable the comparator clear function on PCA  
                                     ///< channel 1.                                    
#define PCA0CLR_CPCE1__ENABLED  0x02 ///< Enable the comparator clear function on PCA   
                                     ///< channel 1.                                    
                                                                                        
#define PCA0CLR_CPCE2__BMASK    0x04 ///< Comparator Clear Enable for CEX2              
#define PCA0CLR_CPCE2__SHIFT    0x02 ///< Comparator Clear Enable for CEX2              
#define PCA0CLR_CPCE2__DISABLED 0x00 ///< Disable the comparator clear function on PCA  
                                     ///< channel 2.                                    
#define PCA0CLR_CPCE2__ENABLED  0x04 ///< Enable the comparator clear function on PCA   
                                     ///< channel 2.                                    
                                                                                        
#define PCA0CLR_CPCPOL__BMASK   0x80 ///< Comparator Clear Polarity                     
#define PCA0CLR_CPCPOL__SHIFT   0x07 ///< Comparator Clear Polarity                     
#define PCA0CLR_CPCPOL__LOW     0x00 ///< PCA channel(s) will be cleared when comparator
                                     ///< result goes logic low.                        
#define PCA0CLR_CPCPOL__HIGH    0x80 ///< PCA channel(s) will be cleared when comparator
                                     ///< result goes logic high.                       
                                                                                        
//------------------------------------------------------------------------------
// PCA0CN0 Enums (PCA Control @ 0xD8)
//------------------------------------------------------------------------------
#define PCA0CN0_CCF0__BMASK   0x01 ///< PCA Module 0 Capture/Compare Flag             
#define PCA0CN0_CCF0__SHIFT   0x00 ///< PCA Module 0 Capture/Compare Flag             
#define PCA0CN0_CCF0__NOT_SET 0x00 ///< A match or capture did not occur on channel 0.
#define PCA0CN0_CCF0__SET     0x01 ///< A match or capture occurred on channel 0.     
                                                                                      
#define PCA0CN0_CCF1__BMASK   0x02 ///< PCA Module 1 Capture/Compare Flag             
#define PCA0CN0_CCF1__SHIFT   0x01 ///< PCA Module 1 Capture/Compare Flag             
#define PCA0CN0_CCF1__NOT_SET 0x00 ///< A match or capture did not occur on channel 1.
#define PCA0CN0_CCF1__SET     0x02 ///< A match or capture occurred on channel 1.     
                                                                                      
#define PCA0CN0_CCF2__BMASK   0x04 ///< PCA Module 2 Capture/Compare Flag             
#define PCA0CN0_CCF2__SHIFT   0x02 ///< PCA Module 2 Capture/Compare Flag             
#define PCA0CN0_CCF2__NOT_SET 0x00 ///< A match or capture did not occur on channel 2.
#define PCA0CN0_CCF2__SET     0x04 ///< A match or capture occurred on channel 2.     
                                                                                      
#define PCA0CN0_CR__BMASK     0x40 ///< PCA Counter/Timer Run Control                 
#define PCA0CN0_CR__SHIFT     0x06 ///< PCA Counter/Timer Run Control                 
#define PCA0CN0_CR__STOP      0x00 ///< Stop the PCA Counter/Timer.                   
#define PCA0CN0_CR__RUN       0x40 ///< Start the PCA Counter/Timer running.          
                                                                                      
#define PCA0CN0_CF__BMASK     0x80 ///< PCA Counter/Timer Overflow Flag               
#define PCA0CN0_CF__SHIFT     0x07 ///< PCA Counter/Timer Overflow Flag               
#define PCA0CN0_CF__NOT_SET   0x00 ///< The PCA counter/timer did not overflow.       
#define PCA0CN0_CF__SET       0x80 ///< The PCA counter/timer overflowed.             
                                                                                      
//------------------------------------------------------------------------------
// PCA0H Enums (PCA Counter/Timer High Byte @ 0xFA)
//------------------------------------------------------------------------------
#define PCA0H_PCA0H__FMASK 0xFF ///< PCA Counter/Timer High Byte
#define PCA0H_PCA0H__SHIFT 0x00 ///< PCA Counter/Timer High Byte
                                                                
//------------------------------------------------------------------------------
// PCA0L Enums (PCA Counter/Timer Low Byte @ 0xF9)
//------------------------------------------------------------------------------
#define PCA0L_PCA0L__FMASK 0xFF ///< PCA Counter/Timer Low Byte
#define PCA0L_PCA0L__SHIFT 0x00 ///< PCA Counter/Timer Low Byte
                                                               
//------------------------------------------------------------------------------
// PCA0MD Enums (PCA Mode @ 0xD9)
//------------------------------------------------------------------------------
#define PCA0MD_ECF__BMASK            0x01 ///< PCA Counter/Timer Overflow Interrupt Enable       
#define PCA0MD_ECF__SHIFT            0x00 ///< PCA Counter/Timer Overflow Interrupt Enable       
#define PCA0MD_ECF__OVF_INT_DISABLED 0x00 ///< Disable the CF interrupt.                         
#define PCA0MD_ECF__OVF_INT_ENABLED  0x01 ///< Enable a PCA Counter/Timer Overflow interrupt     
                                          ///< request when CF is set.                           
                                                                                                 
#define PCA0MD_CPS__FMASK            0x0E ///< PCA Counter/Timer Pulse Select                    
#define PCA0MD_CPS__SHIFT            0x01 ///< PCA Counter/Timer Pulse Select                    
#define PCA0MD_CPS__SYSCLK_DIV_12    0x00 ///< System clock divided by 12.                       
#define PCA0MD_CPS__SYSCLK_DIV_4     0x02 ///< System clock divided by 4.                        
#define PCA0MD_CPS__T0_OVERFLOW      0x04 ///< Timer 0 overflow.                                 
#define PCA0MD_CPS__ECI              0x06 ///< High-to-low transitions on ECI (max rate = system 
                                          ///< clock divided by 4).                              
#define PCA0MD_CPS__SYSCLK           0x08 ///< System clock.                                     
#define PCA0MD_CPS__EXTOSC_DIV_8     0x0A ///< External clock divided by 8 (synchronized with the
                                          ///< system clock).                                    
#define PCA0MD_CPS__LFOSC_DIV_8      0x0C ///< Low frequency oscillator divided by 8.            
                                                                                                 
#define PCA0MD_CIDL__BMASK           0x80 ///< PCA Counter/Timer Idle Control                    
#define PCA0MD_CIDL__SHIFT           0x07 ///< PCA Counter/Timer Idle Control                    
#define PCA0MD_CIDL__NORMAL          0x00 ///< PCA continues to function normally while the      
                                          ///< system controller is in Idle Mode.                
#define PCA0MD_CIDL__SUSPEND         0x80 ///< PCA operation is suspended while the system       
                                          ///< controller is in Idle Mode.                       
                                                                                                 
//------------------------------------------------------------------------------
// PCA0POL Enums (PCA Output Polarity @ 0x96)
//------------------------------------------------------------------------------
#define PCA0POL_CEX0POL__BMASK   0x01 ///< CEX0 Output Polarity 
#define PCA0POL_CEX0POL__SHIFT   0x00 ///< CEX0 Output Polarity 
#define PCA0POL_CEX0POL__DEFAULT 0x00 ///< Use default polarity.
#define PCA0POL_CEX0POL__INVERT  0x01 ///< Invert polarity.     
                                                                
#define PCA0POL_CEX1POL__BMASK   0x02 ///< CEX1 Output Polarity 
#define PCA0POL_CEX1POL__SHIFT   0x01 ///< CEX1 Output Polarity 
#define PCA0POL_CEX1POL__DEFAULT 0x00 ///< Use default polarity.
#define PCA0POL_CEX1POL__INVERT  0x02 ///< Invert polarity.     
                                                                
#define PCA0POL_CEX2POL__BMASK   0x04 ///< CEX2 Output Polarity 
#define PCA0POL_CEX2POL__SHIFT   0x02 ///< CEX2 Output Polarity 
#define PCA0POL_CEX2POL__DEFAULT 0x00 ///< Use default polarity.
#define PCA0POL_CEX2POL__INVERT  0x04 ///< Invert polarity.     
                                                                
//------------------------------------------------------------------------------
// PCA0PWM Enums (PCA PWM Configuration @ 0xF7)
//------------------------------------------------------------------------------
#define PCA0PWM_CLSEL__FMASK             0x07 ///< Cycle Length Select                              
#define PCA0PWM_CLSEL__SHIFT             0x00 ///< Cycle Length Select                              
#define PCA0PWM_CLSEL__8_BITS            0x00 ///< 8 bits.                                          
#define PCA0PWM_CLSEL__9_BITS            0x01 ///< 9 bits.                                          
#define PCA0PWM_CLSEL__10_BITS           0x02 ///< 10 bits.                                         
#define PCA0PWM_CLSEL__11_BITS           0x03 ///< 11 bits.                                         
                                                                                                    
#define PCA0PWM_COVF__BMASK              0x20 ///< Cycle Overflow Flag                              
#define PCA0PWM_COVF__SHIFT              0x05 ///< Cycle Overflow Flag                              
#define PCA0PWM_COVF__NO_OVERFLOW        0x00 ///< No overflow has occurred since the last time this
                                              ///< bit was cleared.                                 
#define PCA0PWM_COVF__OVERFLOW           0x20 ///< An overflow has occurred since the last time this
                                              ///< bit was cleared.                                 
                                                                                                    
#define PCA0PWM_ECOV__BMASK              0x40 ///< Cycle Overflow Interrupt Enable                  
#define PCA0PWM_ECOV__SHIFT              0x06 ///< Cycle Overflow Interrupt Enable                  
#define PCA0PWM_ECOV__COVF_MASK_DISABLED 0x00 ///< COVF will not generate PCA interrupts.           
#define PCA0PWM_ECOV__COVF_MASK_ENABLED  0x40 ///< A PCA interrupt will be generated when COVF is   
                                              ///< set.                                             
                                                                                                    
#define PCA0PWM_ARSEL__BMASK             0x80 ///< Auto-Reload Register Select                      
#define PCA0PWM_ARSEL__SHIFT             0x07 ///< Auto-Reload Register Select                      
#define PCA0PWM_ARSEL__CAPTURE_COMPARE   0x00 ///< Read/Write Capture/Compare Registers at PCA0CPHn 
                                              ///< and PCA0CPLn.                                    
#define PCA0PWM_ARSEL__AUTORELOAD        0x80 ///< Read/Write Auto-Reload Registers at PCA0CPHn and 
                                              ///< PCA0CPLn.                                        
                                                                                                    
//------------------------------------------------------------------------------
// PCON0 Enums (Power Control @ 0x87)
//------------------------------------------------------------------------------
#define PCON0_IDLE__BMASK  0x01 ///< Idle Mode Select                                
#define PCON0_IDLE__SHIFT  0x00 ///< Idle Mode Select                                
#define PCON0_IDLE__NORMAL 0x00 ///< Idle mode not activated.                        
#define PCON0_IDLE__IDLE   0x01 ///< CPU goes into Idle mode (shuts off clock to CPU,
                                ///< but clocks to enabled peripherals are still     
                                ///< active).                                        
                                                                                     
#define PCON0_STOP__BMASK  0x02 ///< Stop Mode Select                                
#define PCON0_STOP__SHIFT  0x01 ///< Stop Mode Select                                
#define PCON0_STOP__NORMAL 0x00 ///< Stop mode not activated.                        
#define PCON0_STOP__STOP   0x02 ///< CPU goes into Stop mode (internal oscillator    
                                ///< stopped).                                       
                                                                                     
#define PCON0_GF0__BMASK   0x04 ///< General Purpose Flag 0                          
#define PCON0_GF0__SHIFT   0x02 ///< General Purpose Flag 0                          
#define PCON0_GF0__NOT_SET 0x00 ///< The GF0 flag is not set. Clear the GF0 flag.    
#define PCON0_GF0__SET     0x04 ///< The GF0 flag is set. Set the GF0 flag.          
                                                                                     
#define PCON0_GF1__BMASK   0x08 ///< General Purpose Flag 1                          
#define PCON0_GF1__SHIFT   0x03 ///< General Purpose Flag 1                          
#define PCON0_GF1__NOT_SET 0x00 ///< The GF1 flag is not set. Clear the GF1 flag.    
#define PCON0_GF1__SET     0x08 ///< The GF1 flag is set. Set the GF1 flag.          
                                                                                     
#define PCON0_GF2__BMASK   0x10 ///< General Purpose Flag 2                          
#define PCON0_GF2__SHIFT   0x04 ///< General Purpose Flag 2                          
#define PCON0_GF2__NOT_SET 0x00 ///< The GF2 flag is not set. Clear the GF2 flag.    
#define PCON0_GF2__SET     0x10 ///< The GF2 flag is set. Set the GF2 flag.          
                                                                                     
#define PCON0_GF3__BMASK   0x20 ///< General Purpose Flag 3                          
#define PCON0_GF3__SHIFT   0x05 ///< General Purpose Flag 3                          
#define PCON0_GF3__NOT_SET 0x00 ///< The GF3 flag is not set. Clear the GF3 flag.    
#define PCON0_GF3__SET     0x20 ///< The GF3 flag is set. Set the GF3 flag.          
                                                                                     
#define PCON0_GF4__BMASK   0x40 ///< General Purpose Flag 4                          
#define PCON0_GF4__SHIFT   0x06 ///< General Purpose Flag 4                          
#define PCON0_GF4__NOT_SET 0x00 ///< The GF4 flag is not set. Clear the GF4 flag.    
#define PCON0_GF4__SET     0x40 ///< The GF4 flag is set. Set the GF4 flag.          
                                                                                     
#define PCON0_GF5__BMASK   0x80 ///< General Purpose Flag 5                          
#define PCON0_GF5__SHIFT   0x07 ///< General Purpose Flag 5                          
#define PCON0_GF5__NOT_SET 0x00 ///< The GF5 flag is not set. Clear the GF5 flag.    
#define PCON0_GF5__SET     0x80 ///< The GF5 flag is set. Set the GF5 flag.          
                                                                                     
//------------------------------------------------------------------------------
// P0 Enums (Port 0 Pin Latch @ 0x80)
//------------------------------------------------------------------------------
#define P0_B0__BMASK 0x01 ///< Port 0 Bit 0 Latch                            
#define P0_B0__SHIFT 0x00 ///< Port 0 Bit 0 Latch                            
#define P0_B0__LOW   0x00 ///< P0.0 is low. Set P0.0 to drive low.           
#define P0_B0__HIGH  0x01 ///< P0.0 is high. Set P0.0 to drive or float high.
                                                                             
#define P0_B1__BMASK 0x02 ///< Port 0 Bit 1 Latch                            
#define P0_B1__SHIFT 0x01 ///< Port 0 Bit 1 Latch                            
#define P0_B1__LOW   0x00 ///< P0.1 is low. Set P0.1 to drive low.           
#define P0_B1__HIGH  0x02 ///< P0.1 is high. Set P0.1 to drive or float high.
                                                                             
#define P0_B2__BMASK 0x04 ///< Port 0 Bit 2 Latch
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
