Agilack/probe-net-serial/ext-display/sw-firmware/display.c

/**
 * NetSerial Display Extention - Character firmware
 *
 * Copyright (c) 2015 Saint-Genest Gwenael <gwen@agilack.fr>
 *
 * This file may be distributed and/or modified under the terms of the
 * GNU General Public License version 2 as published by the Free Software
 * Foundation. (See COPYING.GPL for details.)
 *
 * This file is provided AS IS with NO WARRANTY OF ANY KIND, INCLUDING THE
 * WARRANTY OF DESIGN, MERCHANTABILITY AND FITNESS FOR A PARTICULAR PURPOSE.
 */
#include <efm8bb1.h>
#include "hardware.h"
#include "display.h"
#include "spi.h"
#include "font.h"
#include "splash.h"

static char off_start;

void disp_clear(void)
{
	int i, j;

	for (j = 0; j < 4; j++)
	{
		/* Goto the next line to clear */
		disp_line(j);
		/* Clear the first line */
		for (i = 0; i < 128; i++)
		{
			spi_cs(1);
			spi_wr(0x00);
			spi_cs(0);
		}
	}
}

void disp_draw_front(int en)
{
	/* Set OLED mode to CMD */
	P1_0 = 0;
	
	/* If the "enable" argument is set */
	if (en)
	{
		off_start = 32;
		/* Set Adressing Mode : Horizontal */
		spi_cs(1);
		spi_wr(0x20);
		spi_wr(0x00);
		spi_cs(0);
		/* Set column address */
		spi_cs(1);
		spi_wr(0x21);
		spi_wr(0x00); /* start:  0 */
		spi_wr(0x1F); /* end  : 31 */
		spi_cs(0);
	}
	else
	{
		off_start = 0;
	}
	/* Switch back to data */
	P1_0 = 1;
}

void disp_line(int n)
{
	/* Switch to CND mode */
	P1_0 = 0;
	/* Set Adressing Mode : Page Adressing */
	spi_cs(1);
	spi_wr(0x20);
	spi_wr(0x02);
	spi_cs(0);
	/* Set current page */
	spi_cs(1);
	spi_wr(0xB0 + n);
	spi_cs(0);
	/* Set lower column start address */
	spi_cs(1);
	spi_wr(0x21);
	spi_wr(off_start);
	spi_wr(0x7F);
	spi_cs(0);
	/* Switch back to data */
	P1_0 = 1;
}

void disp_splash(void)
{
	int i;
	
	disp_line(0);
	/* Switch to CMD mode */
	P1_0 = 0;
	/* Set Adressing Mode : Horizontal */
	spi_cs(1);
	spi_wr(0x20);
	spi_wr(0x00);
	spi_cs(0);
	/* Switch back to data */
	P1_0 = 1;
	
	for (i = 0; i < 512; i++)
	{
		spi_cs(1);
		spi_wr( img_splash[i] );
		spi_cs(0);
	}
}

void disp_putc(unsigned char c)
{
	int index;
	int i;
	
	if (c & 0x80)
		return;
	
	index = c - ' ';
	spi_cs(1);
	for (i = 0; i < 8; i++)
		spi_wr( font[index][i] );
	spi_cs(0);
}

void disp_wr(unsigned char v)
{
	spi_cs(1);
	spi_wr(v);
	spi_cs(0);
}

void disp_init(void)
{
	unsigned char i;

	// Set OLED mode to CMD
	P1_0 = 0;

	// Reset the OLED (pulse on RES#)
	P1_1 = 0;
	for (i = 0; i < 0xF0; i++)
		;
	P1_1 = 1;
	for (i = 0; i < 0xF0; i++)
		;

	/* Set Display Off */
	spi_cs(1);
	spi_wr(0xAE);
	spi_cs(0);
	/* Set Clock */
	spi_cs(1);
	spi_wr(0xD5);
	spi_wr(0x80);
	spi_cs(0);
	/* Set Multiplex Ratio */
	spi_cs(1);
	spi_wr(0xA8);
	spi_wr(0x1F);
	spi_cs(0);
	/* Set Display Offset */
	spi_cs(1);
	spi_wr(0xD3);
	spi_wr(0x00);
	spi_cs(0);
	/* Set Display Start Line */
	spi_cs(1);
	spi_wr(0x40);
	spi_cs(0);
	/* Configure Charge Pump  */
	spi_cs(1);
	spi_wr(0x8D);
	spi_wr(0x14);
	spi_cs(0);
	/* Set Segment Remap */
	spi_cs(1);
	spi_wr(0xA1);
	spi_cs(0);
	/* COM pins hardware configuration */
	spi_cs(1);
	spi_wr(0xDA);
	spi_wr(0x00);
	spi_cs(0);
	/* Set Contrast Control */
	spi_cs(1);
	spi_wr(0x81);
	spi_wr(0xCF);
	spi_cs(0);
	/* Set precharge period */
	spi_cs(1);
	spi_wr(0xD9);
	spi_wr(0x1F);
	spi_cs(0);
	/* Set VCOMH deselect level */
	spi_cs(1);
	spi_wr(0xDB);
	spi_wr(0x40);
	spi_cs(0);
	/* Set Entire Display On/Off */
	spi_cs(1);
	spi_wr(0xA4);
	spi_cs(0);
	/* Set Adressing Mode : Page Adressing */
	spi_cs(1);
	spi_wr(0x20);
	spi_wr(0x02);
	spi_cs(0);
	/* Delay ... */
	for (i = 0; i < 0xFF; i++)
		;
	for (i = 0; i < 0xFF; i++)
		;
	/* Set Display On */
	spi_cs(1);
	spi_wr(0xAF);
	spi_cs(0);

	// Set OLED mode to DATA
	P1_0 = 1;

	return;
}
