Agilack/probe-net-serial/ext-display/sw-firmware/splash.h

/**
 * NetSerial Display Extention - Character firmware
 *
 * Copyright (c) 2015 Saint-Genest Gwenael <gwen@agilack.fr>
 *
 * This file may be distributed and/or modified under the terms of the
 * GNU General Public License version 2 as published by the Free Software
 * Foundation. (See COPYING.GPL for details.)
 *
 * This file is provided AS IS with NO WARRANTY OF ANY KIND, INCLUDING THE
 * WARRANTY OF DESIGN, MERCHANTABILITY AND FITNESS FOR A PARTICULAR PURPOSE.
 */
#ifndef SPLASH_H
#define SPLASH_H

/* This buffer contains the static splash screen */
const unsigned char img_splash[512] = {
0xC0, 0xC0, 0x00, 0x00, 0x66, 0xCE, 0x9E, 0x3E, 0x3E, 0x7E, 0xFE, 0xFE, 0xFE, 0xFE, 0xFE, 0xFE, 0xFE, 0xFE, 0xFE, 0xFE, 0xFE, 0xFE, 0xFE, 0xFE, 0xFE, 0xFE, 0xFC, 0xF8, 0xF0, 0xE0, 0xC0, 0x00, 0x00, 0x00, 0x00, 0x00, 0x00, 0x00, 0x00, 0x00, 0x00, 0x00, 0x00, 0x00, 0x00, 0x00, 0x00, 0x00, 0x00, 0x00, 0x00, 0x00, 0x00, 0x00, 0x00, 0x00, 0x00, 0x00, 0x00, 0x00, 0x00, 0x00, 0x00, 0x00, 0x00, 0x00, 0x00, 0x00, 0x00, 0x00, 0x00, 0x00, 0x00, 0x00, 0x00, 0x00, 0x00, 0x00, 0x00, 0x00, 0x00, 0x00, 0x00, 0x00, 0x00, 0x00, 0x00, 0x00, 0x00, 0x00, 0x00, 0x00, 0x00, 0x00, 0x00, 0x00, 0x00, 0x00, 0x00, 0x00, 0x00, 0x00, 0x00, 0x00, 0x00, 0x00, 0x00, 0x00, 0xF8, 0x80, 0x80, 0x00, 0xF0, 0x18, 0x08, 0x18, 0xF0, 0x00, 0x08, 0x00, 0x00, 0x08, 0x18, 0x28, 0x48, 0x88, 0x00, 0x00,
0xFF, 0xFF, 0x00, 0x00, 0xFC, 0xFC, 0xF9, 0xF3, 0xE6, 0xCC, 0x99, 0x33, 0x07, 0x07, 0xE3, 0xF3, 0xFB, 0xF9, 0xF9, 0xF3, 0xE3, 0x07, 0x0F, 0x1F, 0x3F, 0x7F, 0xFF, 0xFF, 0xFF, 0xFF, 0xFF, 0x00, 0x00, 0x00, 0x00, 0x00, 0x00, 0x00, 0x00, 0x00, 0x00, 0x00, 0x00, 0x00, 0x00, 0x00, 0x00, 0x00, 0x00, 0x00, 0x00, 0x00, 0x00, 0x00, 0x00, 0x00, 0x00, 0x00, 0x00, 0x00, 0x00, 0x00, 0x00, 0x00, 0x00, 0x00, 0x00, 0x00, 0x00, 0x00, 0x00, 0x00, 0x00, 0x00, 0x00, 0x00, 0x00, 0x00, 0x00, 0x00, 0x00, 0x00, 0x00, 0x00, 0x00, 0x00, 0x00, 0x00, 0x00, 0x00, 0x00, 0x00, 0x00, 0x00, 0x00, 0x00, 0x00, 0x00, 0x00, 0x00, 0x00, 0x00, 0x00, 0x00, 0x00, 0x00, 0x00, 0x00, 0x00, 0x00, 0x00, 0x00, 0x01, 0x03, 0x02, 0x03, 0x01, 0x00, 0x00, 0x00, 0x00, 0x01, 0x02, 0x02, 0x02, 0x01, 0x00, 0x00, 
0xFF, 0xFF, 0x80, 0x00, 0xFF, 0xFF, 0xFF, 0xFF, 0xFF, 0xFF, 0xFF, 0xFF, 0xFE, 0xFC, 0xF8, 0xF9, 0xF3, 0xF3, 0xF3, 0xF3, 0xF9, 0xFC, 0xF8, 0xF3, 0xE7, 0xCE, 0x9C, 0x39, 0x33, 0x67, 0xCF, 0x80, 0x00, 0x00, 0x00, 0x00, 0x00, 0x00, 0x01, 0xFF, 0x01, 0x80, 0xC0, 0xE0, 0x70, 0x38, 0x1C, 0x0E, 0xFF, 0x00, 0x00, 0x00, 0x7C, 0xFE, 0x93, 0x11, 0x11, 0x11, 0x91, 0xF2, 0x74, 0x00, 0x00, 0x00, 0xFE, 0xFF, 0x01, 0x01, 0x01, 0x02, 0x00, 0x8E, 0xC7, 0xC3, 0xE1, 0x61, 0x61, 0x61, 0x73, 0x3E, 0x1C, 0x00, 0x00, 0x7C, 0xFE, 0x93, 0x11, 0x11, 0x11, 0x91, 0xF2, 0x74, 0x00, 0x00, 0x01, 0xFF, 0xFF, 0x81, 0x00, 0x00, 0x00, 0x80, 0x00, 0x01, 0xFF, 0xFF, 0x01, 0x00, 0x00, 0x1E, 0xBF, 0x31, 0x21, 0x21, 0xA2, 0xFF, 0x7F, 0x01, 0x00, 0x00, 0x01, 0xFF, 0xFF, 0x01, 0x00, 0x00, 0x00, 0x00, 
0x01, 0x03, 0x07, 0x0F, 0x1E, 0x3D, 0x7B, 0x77, 0xEF, 0xCF, 0xCF, 0xCF, 0xCF, 0xCF, 0xCF, 0xCF, 0xCF, 0xCF, 0xCF, 0xCF, 0xCF, 0xCF, 0xCF, 0xCF, 0xCF, 0xCF, 0xCF, 0xCF, 0xCE, 0xCC, 0x08, 0x00, 0x00, 0x00, 0x00, 0x00, 0x00, 0x00, 0x08, 0x0F, 0x07, 0x03, 0x01, 0x00, 0x00, 0x00, 0x00, 0x08, 0x0F, 0x08, 0x00, 0x00, 0x00, 0x00, 0x01, 0x01, 0x01, 0x01, 0x01, 0x00, 0x00, 0x00, 0x00, 0x01, 0x0F, 0x0F, 0x01, 0x01, 0x01, 0x00, 0x00, 0x03, 0x07, 0x0C, 0x08, 0x08, 0x08, 0x08, 0x0C, 0x06, 0x00, 0x00, 0x00, 0x00, 0x00, 0x01, 0x01, 0x01, 0x01, 0x01, 0x00, 0x00, 0x00, 0x00, 0x01, 0x01, 0x01, 0x00, 0x01, 0x01, 0x01, 0x01, 0x00, 0x01, 0x0D, 0x0D, 0x00, 0x00, 0x00, 0x00, 0x00, 0x01, 0x01, 0x01, 0x01, 0x00, 0x00, 0x00, 0x00, 0x00, 0x08, 0x0F, 0x0F, 0x00, 0x00, 0x00, 0x00, 0x00
};

#endif
