Agilack/probe-net-serial/sw-unit_tests/sw-ut_uart-bl/main.c

/**
 * NetSerial - Unit test for UART2 and UART3
 *
 * Copyright (c) 2015 Saint-Genest Gwenael <gwen@agilack.fr>
 *
 * This file may be distributed and/or modified under the terms of the
 * GNU General Public License version 2 as published by the Free Software
 * Foundation. (See COPYING.GPL for details.)
 *
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
 */
#include "hardware.h"
#include "main.h"
#include "time.h"
#include "uart.h"
#include "api.h"

void dma_init(void);
void dma_m2m(char *s, char *d, int len);

int main(void)
{
	api_init();
	
	uart_puts("UARTs 2/3 Unit Test\r\n");
	
	dma_init();
	uart_init();
	
	time_init();
	hw_tim2_init();
	
	uart_puts(" To change speed, type 'a' or 'b' (port), then '0' to '9' (speed)\r\n");
	uart_puts("  Speeds are :\r\n");
	uart_puts("    0 :   1200 bps\r\n");
	uart_puts("    1 :   4800 bps\r\n");
	uart_puts("    2 :   9600 bps (port B default)\r\n");
	uart_puts("    3 :  19200 bps\r\n");
	uart_puts("    4 :  38400 bps\r\n");
	uart_puts("    5 :  57600 bps\r\n");
	uart_puts("    6 : 115200 bps\r\n");
	uart_puts("    7 : 230400 bps\r\n");
	uart_puts("    8 : 460800 bps\r\n");
	uart_puts("    9 : 921600 bps (port A default)\r\n");
	uart_puts("  Example :\r\n");
	uart_puts("    a2 : Set port A to 9600\r\n");
	uart_puts("    b6 : Set port B to 115200\r\n");

	uart2_config(BAUD_921600);
	uart3_config(BAUD_9600);
	while(1)
	{
		uart2_putm("Hello ", 6);
		uart3_putm("World ", 6);
	}
}

void dma_init(void)
{
	/* Activate DMA1 controller */
	reg_set(RCC_AHBENR, 0x01);
}

void dma_m2m(char *s, char *d, int len)
{
	u32 val;
	
	/* Set Peripheral address (destination) */
	reg_wr(DMA_CPAR1, (u32)d );
	/* Set Memory address (source) */
	reg_wr(DMA_CMAR1, (u32)s);
	/* Set number of transfer */
	reg_wr(DMA_CNDTR1, len);
	/* Configure channel */
	val  = (1 << 14); // MEM2MEM
	val |= (3 << 12); // PL   Priority Very High
	val |= (1 <<  7); // MINC Memory Increment Mode
	val |= (1 <<  6); // PINC Peripheral Increment Mode
	val |= (1 <<  4); // DIR  From Memory (to Peripheral)
	reg_wr(DMA_CCR1, val);
	
	/* Activate channel */
	reg_set(DMA_CCR1, 1);
	
	while(1)
	{
		if (reg_rd(DMA_ISR) != 0)
			break;
	}
	reg_clr(DMA_CCR1, 0x01);
	reg_wr(DMA_IFCR, 0x0F);
}
/* EOF */
