Agilack/probe-net-serial/sw-unit_tests/sw-ut_uart-bl/uart.c

/**
 * NetSerial - Unit test for UART2 and UART3
 *
 * Copyright (c) 2015 Saint-Genest Gwenael <gwen@agilack.fr>
 *
 * This file may be distributed and/or modified under the terms of the
 * GNU General Public License version 2 as published by the Free Software
 * Foundation. (See COPYING.GPL for details.)
 *
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
 */
#include "hardware.h"
#include "api.h"
#include "uart.h"

static void uart1_init(void);
static void uart2_init(void);
static void uart3_init(void);

static u8 key;
#ifdef USE_DMA_U1
static u8 u1_rx_buffer[16];
#endif
static u8 u2_rx_buffer[16];
static u8 u3_rx_buffer[16];

void uart_init(void)
{
	key = 0;
	
	uart1_init();
	uart2_init();
	uart3_init();

#ifdef USE_DMA_U1
	reg_clr(UART_CR1(UART1), 0x20); /* Clear RXNEIE bit */
#else
	reg_set(UART_CR1(UART1), 0x20); /* Set RXNEIE bit                */
	reg_set(0xE000E104, 0x20);      /* NVIC: Enable USART1 interrupt */
#endif
}

static void uart1_init(void)
{
#ifdef USE_DMA_U1
	u32 val;
	
	/* Set Peripheral address (source) */
	reg_wr(DMA_CPAR5, UART_DR(UART1) );
	/* Set Memory address (source) */
	reg_wr(DMA_CMAR5, (u32)&u1_rx_buffer);
	/* Set number of transfer */
	reg_wr(DMA_CNDTR5, 16);
	/* Configure channel */
	val  = (2 << 12);   // PL   Priority High
	val |= (1 <<  7);   // MINC Memory Increment Mode
	//val |= (0 <<  4); // DIR  From Peripheral (to Memory)
	reg_wr(DMA_CCR5, val);
	
	/* Set DMAR */
	reg_set(UART_CR3(UART1), 0x40);
	
	/* Activate channel */
	reg_set(DMA_CCR5, 1);
#endif
}

void USART1_IRQHandler(void)   
{
        u32 c;
        c = uart_rd();
        if ((key == 0) && ((c == 'a') || (c == 'A')) )
        {
        	key = 1;
        	uart_puts("Port A");
        	return;
	}
	if ((key == 0) && ((c == 'b') || (c == 'B')) )
	{
		key = 2;
		uart_puts("Port B");
		return;
	}
	if ((key > 0) && (c >= '0') && (c <= '9'))
	{
		u16 speed;
		uart_puts(" => ");
		switch(c)
		{
			case '0': speed = BAUD_1200;   uart_puts("1200");   break;
			case '1': speed = BAUD_4800;   uart_puts("4800");   break;
			case '2': speed = BAUD_9600;   uart_puts("9600");   break;
			case '3': speed = BAUD_19200;  uart_puts("19200");  break;
			case '4': speed = BAUD_38400;  uart_puts("38400");  break;
			case '5': speed = BAUD_57600;  uart_puts("57600");  break;
			case '6': speed = BAUD_115200; uart_puts("115200"); break;
			case '7': speed = BAUD_230400; uart_puts("230400"); break;
			case '8': speed = BAUD_460800; uart_puts("460800"); break;
			case '9': speed = BAUD_921600; uart_puts("921600"); break;
		}
		if (key == 1)
			uart2_config(speed);
		else
			uart3_config(speed);
		uart_puts("\r\n");
        }
        key = 0;
}

static void uart2_init(void)
{
	u32 val;
	
	/* Configure UART2-TX pin (PA2) */
	val  = reg_rd( GPIO_CRL(GPIOA) );
	val &= 0xFFFFF0FF;
	val |= 0x00000B00;
	reg_wr( GPIO_CRL(GPIOA), val);
	/* Configure UART2-RX pin (PA3) */
	val  = reg_rd( GPIO_CRL(GPIOA) );
	val &= 0xFFFF0FFF;
	val |= 0x00004000;
	reg_wr( GPIO_CRL(GPIOA), val);
	/* Activate USART2 */
	reg_set(RCC_APB1ENR, 0x00020000);
	
	reg_wr (UART_BRR(UART2), 0x0120); /* 115200 @ 33.1776MHz  */
	reg_set(UART_CR1(UART2), 0x0C);   /* Set TE & RE bits     */
	reg_set(UART_CR1(UART2), 0x2000); /* Set USART Enable bit */

#ifdef USE_DMA
	/* Set Peripheral address (source) */
	reg_wr(DMA_CPAR7, UART_DR(UART2) );
	/* Configure channel */
	val  = (2 << 12); // PL   Priority High
	val |= (1 <<  7); // MINC Memory Increment Mode
	val |= (1 <<  4); // DIR  From Memory (to Peripheral)
	reg_wr(DMA_CCR7, val);
	
	/* Set DMAT */
	reg_set(UART_CR3(UART2), 0x80);
#endif

#ifdef USE_DMA
	/* Set Peripheral address (source) */
	reg_wr(DMA_CPAR6, UART_DR(UART2) );
	/* Set Memory address (source) */
	reg_wr(DMA_CMAR6, (u32)&u2_rx_buffer);
	/* Set number of transfer */
	reg_wr(DMA_CNDTR6, 16);
	/* Configure channel */
	val  = (2 << 12);   // PL   Priority High
	val |= (1 <<  7);   // MINC Memory Increment Mode
	reg_wr(DMA_CCR6, val);
	
	/* Set DMAR */
	reg_set(UART_CR3(UART2), 0x40);
	
	/* Activate channel */
	reg_set(DMA_CCR6, 1);
#endif
}

static void uart3_init(void)
{
	u32 val;
	
	/* Enable GPIOB */
	reg_set(RCC_APB2ENR, 0x08);
	
	/* Configure UART3-TX pin (PB10) */
	val  = reg_rd( GPIO_CRH(GPIOB) );
	val &= 0xFFFFF0FF;
	val |= 0x00000B00;
	reg_wr( GPIO_CRH(GPIOB), val);
	/* Configure UART3-RX pin (PB11) */
	val  = reg_rd( GPIO_CRH(GPIOB) );
	val &= 0xFFFF0FFF;
	val |= 0x00004000;
	reg_wr( GPIO_CRH(GPIOB), val);
	/* Activate USART3 */
	reg_set(RCC_APB1ENR, 0x00040000);
	
	reg_wr (UART_BRR(UART3), 0x0120); /* 115200 @ 33.1776MHz  */
	reg_set(UART_CR1(UART3), 0x0C);   /* Set TE & RE bits     */
	reg_set(UART_CR1(UART3), 0x2000); /* Set USART Enable bit */

#ifdef USE_DMA
	/* Set Peripheral address (source) */
	reg_wr(DMA_CPAR2, UART_DR(UART3) );
	/* Configure channel */
	val  = (2 << 12); // PL   Priority High
	val |= (1 <<  7); // MINC Memory Increment Mode
	val |= (1 <<  4); // DIR  From Memory (to Peripheral)
	reg_wr(DMA_CCR2, val);
	
	/* Set DMAT */
	reg_set(UART_CR3(UART3), 0x80);
#endif

#ifdef USE_DMA
	/* Set Peripheral address (source) */
	reg_wr(DMA_CPAR3, UART_DR(UART3) );
	/* Set Memory address (source) */
	reg_wr(DMA_CMAR3, (u32)&u3_rx_buffer);
	/* Set number of transfer */
	reg_wr(DMA_CNDTR3, 16);
	/* Configure channel */
	val  = (2 << 12);   // PL   Priority High
	val |= (1 <<  7);   // MINC Memory Increment Mode
	reg_wr(DMA_CCR3, val);
	
	/* Set DMAR */
	reg_set(UART_CR3(UART3), 0x40);
	
	/* Activate channel */
	reg_set(DMA_CCR3, 1);
#endif
}

void uart2_config(u16 speed)
{
	/* baud = 33.1776MHz / (16 * BRR) */
	reg_wr (UART_BRR(UART2), speed);
}

void uart2_putc(u8 c)
{
	while ( (reg_rd(UART_SR(UART2)) & 0x80) != 0x80)
		;
	reg_wr(UART_DR(UART2), c);
}

void uart2_puts(char *s)
{
	while (*s)
	{
		uart2_putc(*s);
		s++;
	}
}

void uart2_putm(char *s, int len)
{
	while ( (reg_rd(UART_SR(UART2)) & 0x80) != 0x80)
		;
	
	/* Set Memory address (source) */
	reg_wr(DMA_CMAR7, (u32)s);
	/* Set number of transfer */
	reg_wr(DMA_CNDTR7, len);
	
	/* Activate channel */
	reg_set(DMA_CCR7, 1);

	/* DEBUG : wait synchronously has poor performance */
	while(1)
	{
		if (reg_rd(DMA_ISR) & 0x0A000000)
			break;
	}
	/* Desactivate channel */
	reg_clr(DMA_CCR7, 0x01);
	/* Clear interrupts for channel */
	reg_wr(DMA_IFCR,  0x0F000000);
}

inline int uart2_isready(void)
{
	return (reg_rd(UART_SR(UART2)) & 0x20);
}

inline int uart2_rd(void)
{
	return (reg_rd(UART_DR(UART2)) & 0xFF);
}

void uart3_config(u16 speed)
{
	/* baud = 33.1776MHz / (16 * BRR) */
	reg_wr (UART_BRR(UART3), speed);
}

void uart3_putc(u8 c)
{
	while ( (reg_rd(UART_SR(UART3)) & 0x80) != 0x80)
		;
	reg_wr(UART_DR(UART3), c);
}

void uart3_puts(char *s)
{
	while (*s)
	{
		uart3_putc(*s);
		s++;
	}
}

void uart3_putm(char *s, int len)
{
	while ( (reg_rd(UART_SR(UART3)) & 0x80) != 0x80)
		;
	
	/* Set Memory address (source) */
	reg_wr(DMA_CMAR2, (u32)s);
	/* Set number of transfer */
	reg_wr(DMA_CNDTR2, len);
	
	/* Activate channel */
	reg_set(DMA_CCR2, 1);

	/* DEBUG : wait synchronously has poor performance */
	while(1)
	{
		if (reg_rd(DMA_ISR) & 0x000000A0)
			break;
	}
	/* Desactivate channel */
	reg_clr(DMA_CCR2, 0x01);
	/* Clear interrupts for channel */
	reg_wr(DMA_IFCR,  0x000000F0);
}

inline int uart3_isready(void)
{
	return (reg_rd(UART_SR(UART3)) & 0x20);
}

inline int uart3_rd(void)
{
	return (reg_rd(UART_DR(UART3)) & 0xFF);
}

int uart_isready(void)
{
	return (reg_rd(UART_SR(UART1)) & 0x20);
}
int uart_rd(void)
{
	return (reg_rd(UART_DR(UART1)) & 0xFF);
}
void uart_crlf (void)
{
	uart_putc('\r');
	uart_putc('\n');
}
/* EOF */
