Agilack/probe-net-serial/ext-display/sw-unit_test/sw-ut_oled/img.h

/**
 * NetSerial Display Extention - Unit test
 *
 * Copyright (c) 2015 Saint-Genest Gwenael <gwen@agilack.fr>
 *
 * This file may be distributed and/or modified under the terms of the
 * GNU General Public License version 2 as published by the Free Software
 * Foundation. (See COPYING.GPL for details.)
 *
 * This file is provided AS IS with NO WARRANTY OF ANY KIND, INCLUDING THE
 * WARRANTY OF DESIGN, MERCHANTABILITY AND FITNESS FOR A PARTICULAR PURPOSE.
 */
#ifndef IMG_H
#define IMG_H

/* This buffer contains a static image */
const unsigned char img_p1[512] = {
0x00, 0xc0, 0x80, 0x00, 0x60, 0xc4, 0x8c, 0x1c, 0x3c, 0x7c, 0xfc, 0xfc, 0xfc, 0xfc, 0xfc, 0xfc, 0xfc, 0xfc, 0xfc, 0xfc, 0xfc, 0xfc, 0xfc, 0xfc, 0xfc, 0xfc, 0xf8, 0xf0, 0xe0, 0xc0, 0x00, 0x00, 0x00, 0x00, 0x00, 0x00, 0x00, 0x00, 0x00, 0x00, 0x00, 0x00, 0x00, 0x00, 0x00, 0x00, 0x00, 0x00, 0x00, 0x00, 0x00, 0x00, 0x00, 0x00, 0x00, 0x00, 0x00, 0x00, 0x00, 0x00, 0x00, 0x00, 0x00, 0x00, 0x00, 0x00, 0x00, 0x00, 0x00, 0x00, 0x00, 0x00, 0x00, 0x00, 0x00, 0x00, 0x00, 0xf0, 0xfe, 0x1e, 0xfe, 0xf0, 0x00, 0x00, 0x00, 0xf0, 0xfe, 0x1e, 0xfe, 0xf0, 0x00, 0x00, 0x00, 0xf0, 0xfc, 0x0c, 0x06, 0x06, 0x06, 0x06, 0x0c, 0xfc, 0xf0, 0x00, 0x00, 0xfe, 0xfe, 0x00, 0x00, 0x00, 0x00, 0x00, 0x00, 0xfe, 0xfe, 0x00, 0x00, 0xf8, 0xfc, 0x0e, 0x06, 0x06, 0x06, 0x0c, 0xfe, 0xfe, 0x00, 0x00, 
0x00, 0xff, 0xff, 0x00, 0xfe, 0xfc, 0xf9, 0xf3, 0xe6, 0xcc, 0x98, 0x31, 0x03, 0x07, 0xe3, 0xf3, 0xf1, 0xf1, 0xf3, 0xe3, 0x07, 0x0f, 0x9f, 0x3f, 0x7f, 0xff, 0xff, 0xff, 0xff, 0xff, 0x00, 0x00, 0x00, 0x00, 0x00, 0x00, 0x00, 0x00, 0x00, 0x00, 0x00, 0x00, 0x00, 0x00, 0x00, 0x00, 0x00, 0x00, 0x00, 0x00, 0x00, 0x00, 0x00, 0x00, 0x00, 0x00, 0x00, 0x00, 0x00, 0x00, 0x00, 0x00, 0x00, 0x00, 0x00, 0x00, 0x00, 0x00, 0x00, 0x00, 0x00, 0x00, 0x00, 0x00, 0x00, 0x30, 0x3f, 0x0f, 0x00, 0x00, 0x00, 0x0f, 0x3f, 0x38, 0x3f, 0x0f, 0x00, 0x00, 0x00, 0x0f, 0x3f, 0x30, 0x00, 0x00, 0x03, 0x03, 0x06, 0x06, 0x06, 0x06, 0x03, 0x03, 0x00, 0x00, 0x00, 0x07, 0x07, 0x03, 0x06, 0x06, 0x06, 0x00, 0x00, 0x7f, 0x7f, 0x00, 0x00, 0x01, 0x03, 0x07, 0x06, 0x06, 0x06, 0x03, 0x7f, 0x7f, 0x00, 0x00, 
0x00, 0xff, 0xff, 0x80, 0x7f, 0xff, 0xff, 0xff, 0xff, 0xff, 0xff, 0xff, 0xfe, 0xfc, 0xf8, 0xf1, 0xf3, 0xf3, 0xf1, 0xf9, 0xf8, 0xf8, 0xf1, 0xe3, 0xc6, 0x8c, 0x19, 0x33, 0x67, 0xcf, 0x00, 0x00, 0x00, 0x00, 0x00, 0x00, 0xfe, 0xfe, 0x80, 0x80, 0x80, 0x80, 0x80, 0x80, 0xfe, 0xfe, 0x00, 0x00, 0x00, 0xf0, 0xfc, 0x6c, 0x66, 0x66, 0x66, 0x66, 0x66, 0xe6, 0xec, 0x00, 0x00, 0xfe, 0xfe, 0x00, 0x00, 0x00, 0xfe, 0xfe, 0x00, 0x00, 0xf0, 0xfc, 0x0c, 0x06, 0x06, 0x06, 0x06, 0x0c, 0xfc, 0xf0, 0x00, 0x00, 0x00, 0x00, 0x00, 0x00, 0x00, 0x00, 0x00, 0x00, 0x00, 0x00, 0x00, 0x00, 0x00, 0x00, 0x00, 0x00, 0x00, 0x00, 0x00, 0x00, 0x00, 0x00, 0x00, 0x00, 0x00, 0x00, 0x00, 0x00, 0x00, 0x00, 0x00, 0x00, 0x00, 0x00, 0x00, 0x00, 0x00, 0x00, 0x00, 0x00, 0x00, 0x00, 0x00, 0x00, 0x00, 0x00, 
0x00, 0x00, 0x01, 0x03, 0x07, 0x0e, 0x1d, 0x3b, 0x77, 0x77, 0x77, 0x77, 0x77, 0x77, 0x77, 0x77, 0x77, 0x77, 0x77, 0x77, 0x77, 0x77, 0x77, 0x77, 0x77, 0x77, 0x77, 0x76, 0x04, 0x00, 0x00, 0x00, 0x00, 0x00, 0x00, 0x00, 0x3f, 0x3f, 0x01, 0x01, 0x01, 0x01, 0x01, 0x01, 0x3f, 0x3f, 0x00, 0x00, 0x00, 0x00, 0x03, 0x03, 0x06, 0x06, 0x06, 0x06, 0x07, 0x03, 0x01, 0x00, 0x00, 0x7f, 0x7f, 0x00, 0x00, 0x00, 0x7f, 0x7f, 0x00, 0x00, 0x00, 0x03, 0x03, 0x06, 0x06, 0x06, 0x06, 0x03, 0x03, 0x00, 0x00, 0x00, 0x00, 0x00, 0x00, 0x00, 0x00, 0x00, 0x00, 0x00, 0x00, 0x00, 0x00, 0x00, 0x00, 0x00, 0x00, 0x00, 0x00, 0x00, 0x00, 0x00, 0x00, 0x00, 0x00, 0x00, 0x00, 0x00, 0x00, 0x00, 0x00, 0x00, 0x00, 0x00, 0x00, 0x00, 0x00, 0x00, 0x00, 0x00, 0x00, 0x00, 0x00, 0x00, 0x00, 0x00, 0x00, 0x00
};

#endif
