Agilack/probe-net-serial/sw-unit_tests/sw-ut_eth_uip/net/uip-conf.h

/*
 * Copyright (c) 2006, Swedish Institute of Computer Science.
 * All rights reserved.
 *
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
 * This file is part of the uIP TCP/IP stack
 *
 * $Id: uip-conf.h,v 1.6 2006/06/12 08:00:31 adam Exp $
 */
#ifndef __UIP_CONF_H__
#define __UIP_CONF_H__

#include <stdint.h>

#define UIP_CONF_EXTERNAL_BUFFER

/**
 * 8 bit datatype
 *
 * This typedef defines the 8-bit type used throughout uIP.
 *
 * \hideinitializer
 */
typedef uint8_t u8_t;

/**
 * 16 bit datatype
 *
 * This typedef defines the 16-bit type used throughout uIP.
 *
 * \hideinitializer
 */
typedef uint16_t u16_t;

/**
 * Statistics datatype
 *
 * This typedef defines the dataype used for keeping statistics in
 * uIP.
 *
 * \hideinitializer
 */
typedef unsigned short uip_stats_t;

/**
 * Maximum number of TCP connections.
 *
 * \hideinitializer
 */
#define UIP_CONF_MAX_CONNECTIONS 10

/**
 * Maximum number of listening TCP ports.
 *
 * \hideinitializer
 */
#define UIP_CONF_MAX_LISTENPORTS 10

/**
 * uIP buffer size.
 *
 * \hideinitializer
 */
#define UIP_CONF_BUFFER_SIZE     1480

/**
 * CPU byte order.
 *
 * \hideinitializer
 */
#define UIP_CONF_BYTE_ORDER      LITTLE_ENDIAN

/**
 * Logging on or off
 *
 * \hideinitializer
 */
#define UIP_CONF_LOGGING         0

/**
 * UDP support on or off
 *
 * \hideinitializer
 */
#define UIP_CONF_UDP             0

/**
 * UDP checksums on or off
 *
 * \hideinitializer
 */
#define UIP_CONF_UDP_CHECKSUMS   1

/**
 * uIP statistics on or off
 *
 * \hideinitializer
 */
#define UIP_CONF_STATISTICS      1

#define PACK_STRUCT_END

/* Here we include the header file for the application(s) we use in
   our project. */
/*#include "smtp.h"*/
/*#include "hello-world.h"*/
/*#include "telnetd.h"*/
/*#include "webserver.h"*/
/*#include "dhcpc.h"*/
/*#include "resolv.h"*/
/*#include "webclient.h"*/
#include "eth_app.h"

#endif /* __UIP_CONF_H__ */
